OETSolutions/e-ink-weather/work/cad/bez_front.png

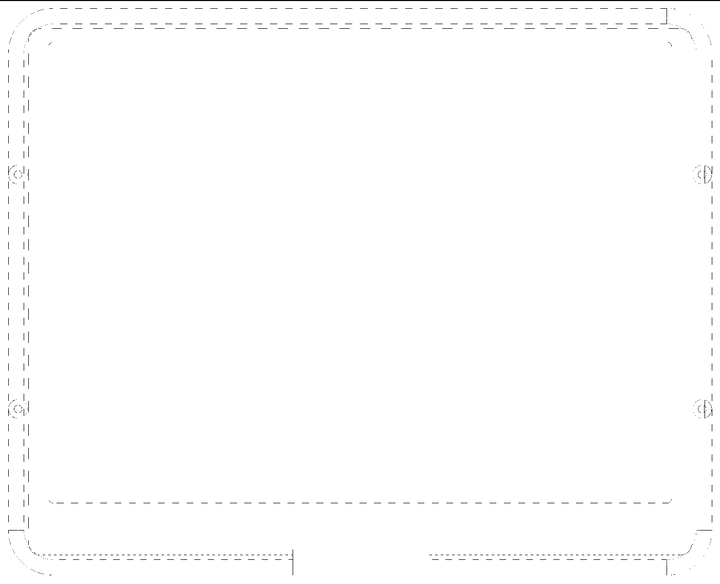
work/cad/bez_front.png
