OETSolutions/e-ink-weather/work/cad/body_iso.png

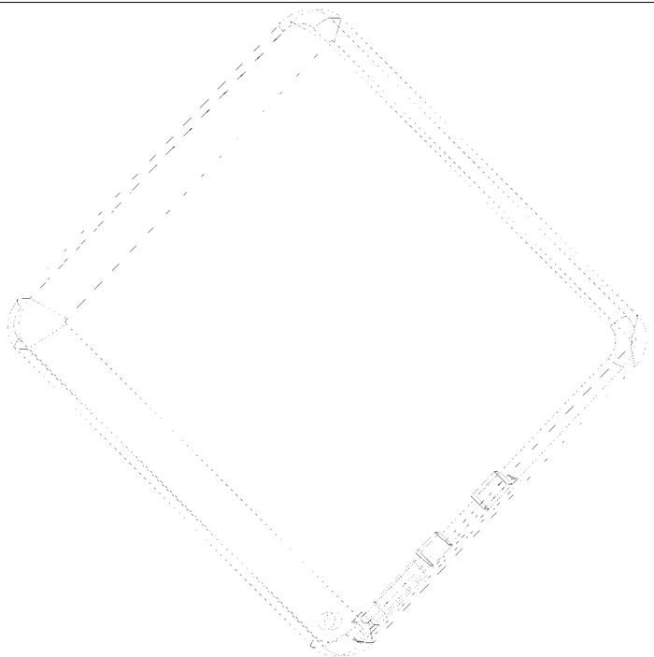
work/cad/body_iso.png
