OETSolutions/e-ink-weather/work/cad/body_side.png

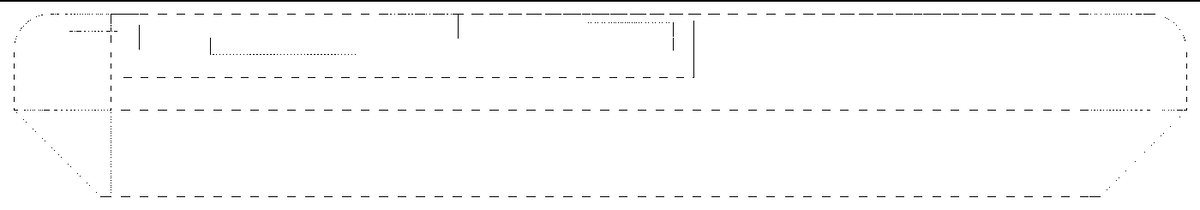
work/cad/body_side.png
