OETSolutions/e-ink-weather/work/cad/ch_iso.png

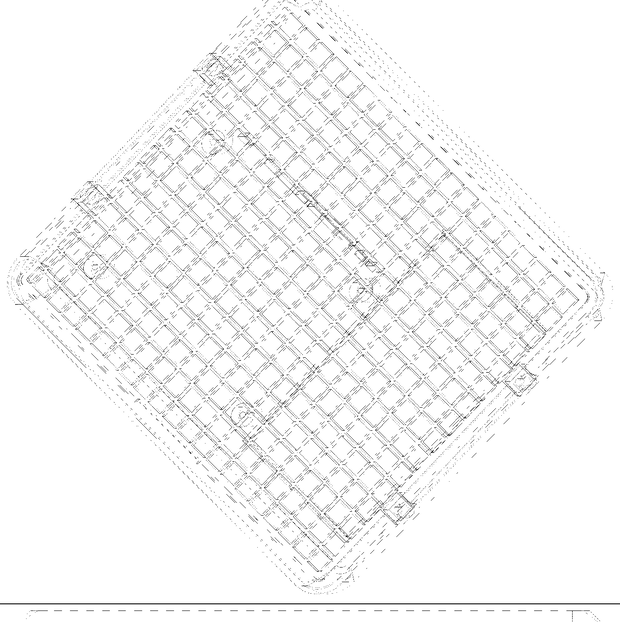
work/cad/ch_iso.png
