OETSolutions/e-ink-weather/work/cad/panel_front.png

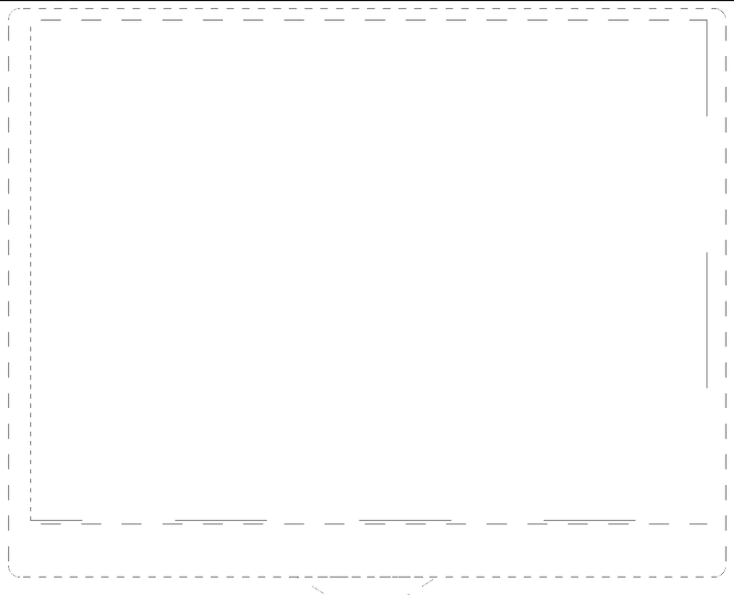
work/cad/panel_front.png
