OETSolutions/e-ink-weather/work/cad/shell_iso2_zoom.png

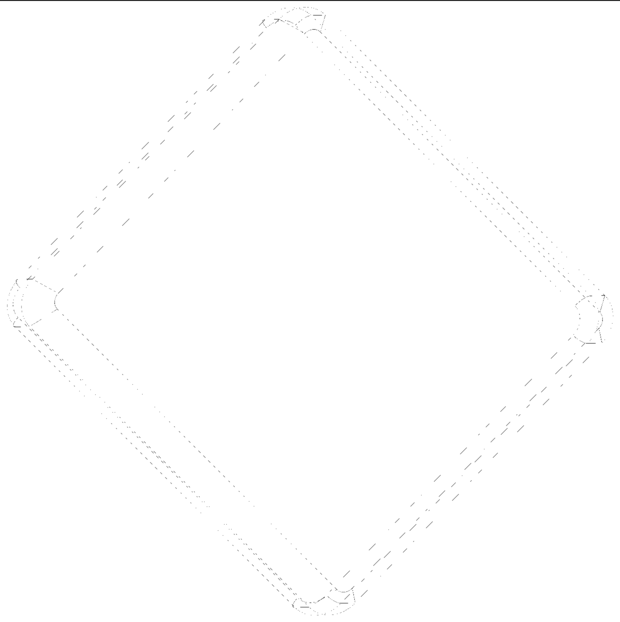
work/cad/shell_iso2_zoom.png
