OETSolutions/e-ink-weather/work/cad/shell_iso_zoom.png

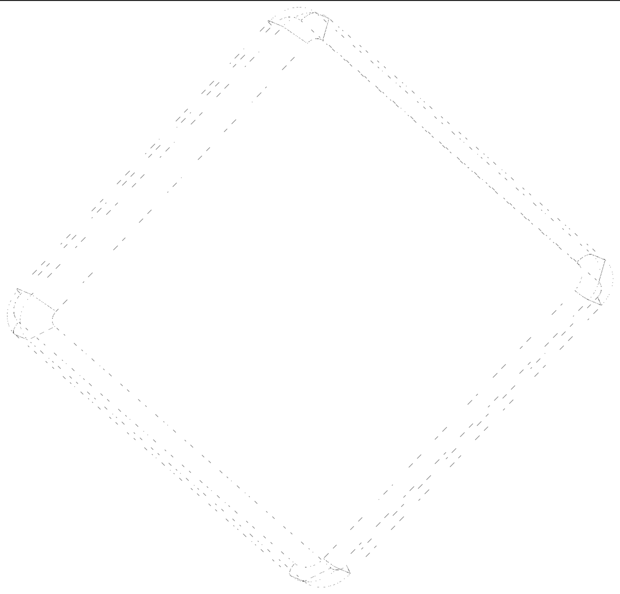
work/cad/shell_iso_zoom.png
