OETSolutions/e-ink-weather/work/cad/shell_side2.png

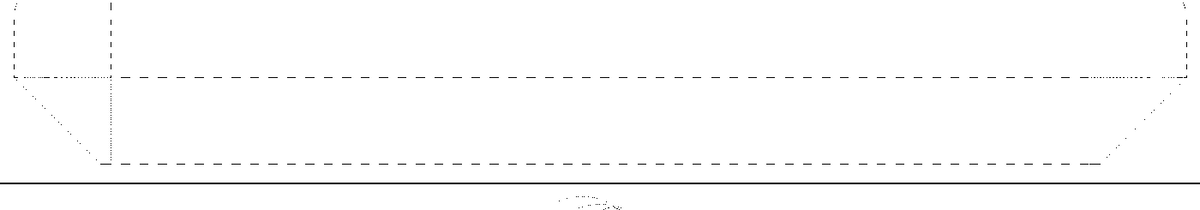
work/cad/shell_side2.png
