OETSolutions/e-ink-weather/work/cad/front_frame.FCStd

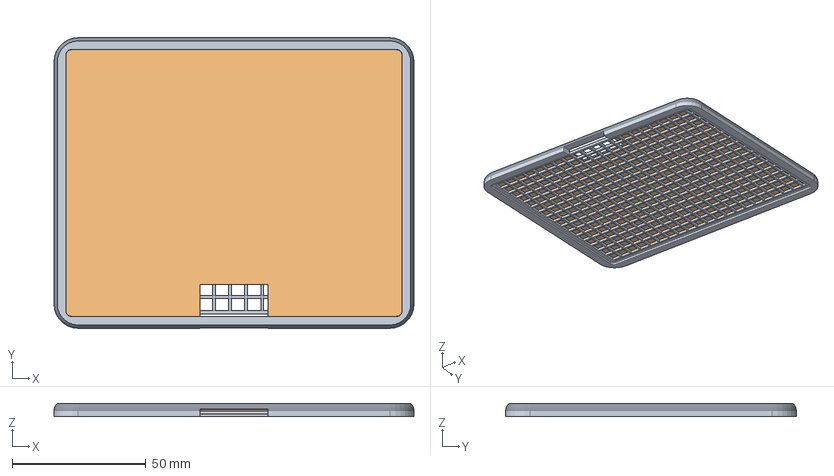
[picture p30: CAD file, 2026-09-19]
work/cad/front_frame.FCStd
134.4 x 108.5 x 4.80 mm
PRINT: Front frame + support grid
CUT: 0.5 mm closed-cell foam backing
