OETSolutions/e-ink-weather/work/cad/panel.FCStd

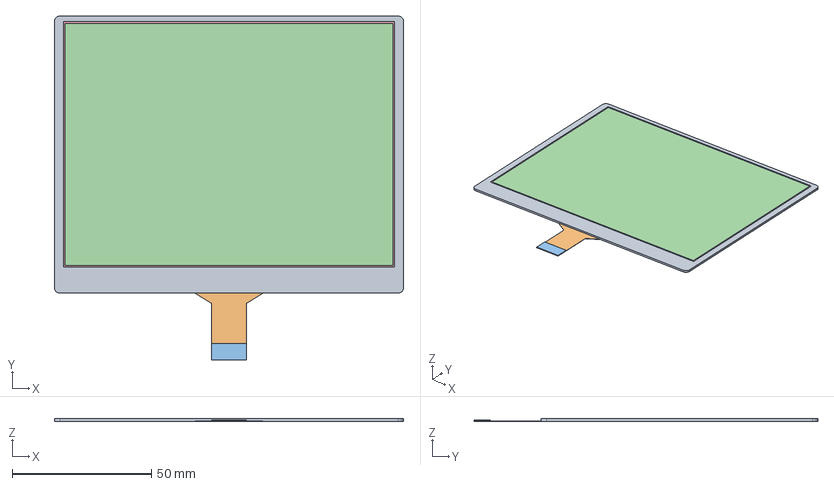
[picture p31: CAD file, 2026-09-19]
work/cad/panel.FCStd
125.4 x 123.5 x 0.902 mm
PANEL_GLASS
PANEL_FPC_TAIL
PANEL_FPC_STIFFENER
PANEL_ACTIVE_AREA
PANEL_BORDER
