OETSolutions/e-ink-weather/code/firmware/components/app/app_refresh.c

#include "app_refresh.h"
#include "api.h"
#include "api_store.h"
#include "canvas.h"
#include "cfg_store.h"
#include "cJSON.h"
#include "datasrc.h"
#include "devcfg.h"
#include "epd.h"
#include "fonts.h"
#include "geo_ip.h"
#include "ha.h"
#include "layout_model.h"
#include "net_http.h"
#include "net_wifi.h"
#include "nvs_keys.h"
#include "owm.h"
#include "provscreen.h"
#include "prov.h"
#include "refresh_policy.h"
#include "render.h"
#include "thermal_guard.h"
#include "value_resolve.h"
#include "widgets.h"
#include "esp_heap_caps.h"
#include "heap_trace.h"
#include "freertos/FreeRTOS.h"
#include "freertos/task.h"
#include "esp_log.h"
#include "esp_system.h"
#include "esp_timer.h"
#include "nvs.h"
#include <string.h>
#include <stdlib.h>

/* The vendor demo reference image, used as the static layer until the web app has uploaded
 * one (Task 21). Declared here rather than included, because it lives in src/ and this is a
 * component — and because it is a placeholder to be deleted, so the dependency should be
 * one line, not an include path. */
/* The boot mark shown when no layout bitmap has been uploaded yet. Generated from the
 * OETSolutions / Aether artwork by tools/gen_boot_logo.py — see that script for the pipeline.
 * This replaced the vendor GoodDisplay demo image, which had no business on a shipped
 * device: it was a bring-up baseline, not artwork. */
extern const uint8_t boot_logo[EPD_FB_BYTES];
/* The header-sized version of the same mark, for the provisioning screen. Generated together
 * with the splash so the two cannot drift apart. */
extern const uint8_t boot_badge[];
extern const int boot_badge_w;
extern const int boot_badge_h;

static const char *TAG = "refresh";

/* How long ensure_static() waits for the freed static-layer region to coalesce before giving up
 * on a tick.
 *
 * MEASURED, NOT GUESSED. When the region is fragmented by a network allocation sitting in the
 * middle of it, the largest free block reads 77,824 — 376 bytes SHORT of the 78,200 a
 * framebuffer needs — and the block walk shows the fragmenter is a handful of 28..132-byte
 * network-stack allocations that free on their own. The pieces then coalesce into one
 * 78,380-byte block, which DOES fit, but the coalesce is not instant: under sustained 2 s HTTP
 * churn the wait was measured acquiring on attempts 16..29, i.e. 800..1,450 ms, with the FIRST
 * acquisition needing longer than the old 5 s ceiling in the worst observed case. So 5 s was
 * marginal and 15 s is a comfortable margin over a 1.45 s measurement.
 *
 * A tick that still cannot get its frame keeps the previous image on the glass, which is the
 * correct FR-29 behaviour, and it RETRIES shortly (see the retry in app_refresh_tick) rather
 * than waiting a whole interval — a stale panel for 15 minutes is the real cost being avoided.
 * On battery this loop is never entered under normal use: the radio is torn down before the
 * render window, so the region is already clean. */
#define FB_ACQUIRE_WAIT_MS 15000
#define FB_ACQUIRE_POLL_MS 50

/* The slot identity meaning "no picture is known to be on the glass", i.e. a partial has no valid
 * base. The three identity spaces are kept disjoint BY CONSTRUCTION:
 *
 *   per-page artwork   -(100 + page*100 + seq)  with page 0..7 and seq 0..99  => -100 .. -899
 *   the legacy bitmap  its live slot number (0 or 1)
 *   the built-in mark  SLOT_BOOT_LOGO (-1000)
 *   unknown            SLOT_NONE (-1)
 *
 * The artwork range has room for 8 pages x 100 sequences, and ARTWORK_MAX_PAGES is 8, so the spaces
 * cannot overlap for any real layout. (An earlier draft used -(100 + page), which left no room for
 * the sequence and collided with the boot mark at page 1 — see load_static_layer_seg for why the
 * sequence is required.)
 *
 * The distinction from SLOT_NONE matters and is NOT a sign test: the artwork sentinel is NEGATIVE,
 * so `slot < 0` is true for every real uploaded layout. See s_shown_slot. */
#define SLOT_NONE      (-1)
#define SLOT_BOOT_LOGO (-1000)

/* The fields to stamp one refresh, and their values. Sized by the parse caps rather than allocated.
 * This is the TICK-LOCAL page, which also carries the parsed widgets and the FR-27 reporting arrays;
 * only the three members a render needs are copied into the cross-tick snapshot below. */
typedef struct {
    layout_widget_t widgets[LAYOUT_MAX_FIELDS];
    value_field_t   fields[LAYOUT_MAX_FIELDS];
    char            values[LAYOUT_MAX_FIELDS][LAYOUT_VALUE_BUF];
    const char     *value_ptrs[LAYOUT_MAX_FIELDS];
    /* The widget id, the RAW reading and whether the drawn string is that number's plain
     * rendering, parallel to values/fields, so GET /api/values (FR-27) can report which box each
     * resolved string belongs to AND let the editor re-format it locally after a format edit. The
     * id is copied rather than pointed at: the widget array is overwritten by the next refresh.
     * `readings`/`rendered_number` are only populated for widgets whose value drew the number —
     * see value_format_widget_rendered(). */
    char            ids[LAYOUT_MAX_FIELDS][API_VALUES_ID_LEN];
    int             has_value[LAYOUT_MAX_FIELDS];
    int             rendered_number[LAYOUT_MAX_FIELDS];
    double          readings[LAYOUT_MAX_FIELDS];
    int             n;              /* how many the page asked for */
    int             n_fields;       /* how many are actually stamped (dynamic only) */
} page_render_t;

/* JUST THE DRAWABLE HALF OF A PAGE: the boxes, their strings, and the count.
 *
 * WHY THIS IS A SEPARATE, SMALL TYPE. The previous frame must be reproducible across ticks, and
 * page_render_t is 9,320 bytes because it also carries the parsed widgets (24 x 288) and the
 * FR-27 reporting arrays — none of which a render reads. Keeping one of those resident costs
 * ~9 KB of .bss, and .bss on this part is DRAM the heap does not get: measured, adding a 9,320-byte
 * static here dropped the largest free block below the 78,200 bytes the static layer needs, so
 * NOTHING could be drawn. The drawable half is 1,640 bytes, which fits. */
typedef struct {
    value_field_t fields[LAYOUT_MAX_FIELDS];
    char          values[LAYOUT_MAX_FIELDS][LAYOUT_VALUE_BUF];
    const char   *value_ptrs[LAYOUT_MAX_FIELDS];
    int           n_fields;
} frame_values_t;

/* What a render needs, pointing at either a live page or the snapshot. `values` is `const char **`
 * rather than `const char *const *` so a live page's array can be used without a cast. */
typedef struct {
    const value_field_t *fields;
    const char *const   *values;
    int                  n_fields;
} frame_spec_t;

/* ONE 78,200-byte buffer, holding the STATIC LAYER of the page currently on the glass — not the
 * composed frame.
 *
 * WHY THE STATIC LAYER AND NOT THE FRAME: a partial refresh passes the SSD2677 the previous and
 * the next frame, because it derives each pixel's transition from the pair. Two frames of 78,200
 * bytes do not fit this part — the only DRAM region large enough for one is 113,840 bytes and the
 * pair needs 156,400 — so a second framebuffer NEVER allocated. Measured on the bench: the
 * transient allocation failed on every refresh and /api/status read `partials_since_full: 0`
 * against `fulls_total: 6`, so FR-11's partial path had never run and every refresh was a full
 * panel flash.
 *
 * Holding the static layer instead makes both frames derivable from ONE buffer: the previous frame
 * is this layer stamped with s_prev_values' strings, and the next frame is the same layer stamped
 * with the current page's values. A partial is only ever taken when the slot identity matches,
 * which means the two frames genuinely share this layer — so it is the right thing to keep.
 *
 * HELD AS SEGMENTS, NOT ONE CONTIGUOUS BUFFER, and that is the whole fix for the render-OOM report
 * (2026-09-22). A single 78,200-byte allocation needs the ONE DRAM region large enough to hold it
 * (0x3ffe4350, 113,840 bytes), and while the HTTP API is live that region is fragmented below
 * 78,200 by a persistent 8,192-byte httpd task stack plus a 16,384-byte app task stack — neither
 * frees, so no wait helps. Held as ~16 KB segments the same bytes come from pieces that always fit
 * (measured: 32,768 bytes allocated fine at the exact moment a 78,200-byte request failed). See
 * segbuf.h.
 *
 * Allocated lazily and FREED ACROSS EVERY FETCH (see app_refresh_tick): the fetch needs contiguous
 * room the segments would otherwise occupy, and a fetch that fails leaves every reading as "--".
 *
 * FREED HERE RATHER THAN IN .bss: as a static array the segments' POINTERS would sit in DRAM that
 * the heap does not get — see the note on the band buffers. */
static segbuf_t s_layer;

/* The strip decoder's state (~11 KB), reserved BY ensure_static() before the segments and released
 * once the layer is loaded (see api_store.h for why the ORDER matters: allocated lazily during the
 * decode it intermittently finds no hole and the strip silently fails). */
static artwork_inflate_t *s_inflate;

/* A segment allocator and releaser for s_layer. Plain internal DRAM, the same capability the old
 * contiguous allocation used. */
static void *layer_seg_alloc(size_t n) { return heap_caps_malloc(n, MALLOC_CAP_8BIT); }
static void  layer_seg_free(void *p)   { free(p); }
/* The identity of the picture on the glass, from load_static_layer_seg(): a NEGATIVE sentinel for
 * per-page artwork (-(100 + page*100 + seq)), the bitmap's slot for the legacy single bitmap, SLOT_BOOT_LOGO
 * for the built-in boot mark, SLOT_NONE when nothing is known. Compared for equality to decide
 * whether a partial is valid.
 *
 * IT MUST NOT DOUBLE AS THE "IS ANYTHING ON THE GLASS" FLAG, and that is a bug this code had: the
 * artwork sentinel is negative, so `s_shown_slot < 0` was true for every real uploaded layout and
 * every tick read "nothing on the glass" and forced a FULL refresh — which is exactly why
 * /api/status showed `partials_since_full: 0` no matter what the partial budget said. The two
 * questions are different and now have different answers: identity here, presence in
 * s_glass_present below. */
static int      s_shown_slot = SLOT_NONE;
/* Non-zero once a push has put an image on the glass and nothing has overwritten or dropped it
 * since. This, not the sign of the slot, is what refresh_decide() means by "something is on the
 * glass to diff against". */
static int      s_glass_present;

/**
 * Static layer ownership: one mutex guarding the 78,200-byte resident layer.
 *
 * WHY THIS EXISTS. The OTA path opens a TLS connection from an HTTP handler — the httpd task —
 * while the render task holds the layer resident between ticks. The handshake needs the ONE
 * contiguous DRAM region large enough for a framebuffer (see the release reasoning below), so
 * with the layer held it fails outright:
 *
 *     esp-tls-mbedtls: mbedtls_ssl_setup returned -0x7F00   (ALLOC_FAILED)
 *     api_ota: manifest fetch failed: ESP_ERR_HTTP_CONNECT
 *
 * measured on the bench 2026-09-24 — every OTA check returned 502 in ~0.12 s, which is the
 * tell that no handshake was ever attempted. The refresh path avoids this by releasing the
 * layer before its own fetches; the OTA handlers cannot, because they run on a DIFFERENT task
 * and must not free memory the render task is in the middle of reading.
 *
 * So ownership is explicit: the whole tick holds this lock, and a fetcher outside the render
 * path takes it (waiting for any tick in flight), drops the layer, does its TLS work, and gives
 * it back. One lock, one rule — see app_fetch_pause().
 */
static SemaphoreHandle_t s_layer_mutex;

static void layer_lock(void)
{
    /* Created on first use rather than in app_main: this file has no init function and the
     * first caller may be either task. xSemaphoreCreateMutex has no failure mode worth
     * branching on here beyond allocation, and a failure to allocate a mutex on a heap that
     * must hold a 78 KB framebuffer means the device has far larger problems. */
    if (!s_layer_mutex) {
        static portMUX_TYPE mux = portMUX_INITIALIZER_UNLOCKED;
        portENTER_CRITICAL(&mux);
        if (!s_layer_mutex) s_layer_mutex = xSemaphoreCreateMutex();
        portEXIT_CRITICAL(&mux);
    }
    if (s_layer_mutex) xSemaphoreTake(s_layer_mutex, portMAX_DELAY);
}

static void layer_unlock(void)
{
    if (s_layer_mutex) xSemaphoreGive(s_layer_mutex);
}

/* Every return in the tick must land here so the layer is never left un-released on an error
 * path — a layer held by a returned tick would block every later fetch pause. */

/* The values that were stamped into the frame now on the glass, so the PREVIOUS frame can be
 * recomposed for a partial. This is the whole reason a partial is possible here: the previous
 * frame is not stored (two frames do not fit), it is REPRODUCED from the resident static layer
 * plus these values, and 24 strings of 40 bytes is 1.6 KB rather than 78,200. */
static frame_values_t s_prev_values;
static int            s_have_prev_values;   /* 0 until a push has recorded what it drew */

/* Allocate the resident static layer, as SEGMENTS. Returns 0 on success, -1 on failure.
 *
 * SEGMENTATION IS THE FIX for the render-OOM report: a single 78,200-byte request needs the one
 * DRAM region large enough to hold it, and the live HTTP API fragments that region below 78,200
 * with allocations that never free. Small segments are always placeable. The sizes are tried
 * largest-first (16 KB down to 2 KB) so the common case keeps the segment count low and the band
 * reader's inner loop short; a fragmented heap simply settles on smaller pieces.
 *
 * NO INFLATE WINDOW IS RESERVED HERE. The artwork is stored as independent per-strip zlib streams
 * (see lib/upload/artwork.h), so loading it needs no 32 KB dictionary: only a strip-sized output
 * buffer and a ~11 KB decompressor that lives on the caller's stack. An earlier single-stream
 * version reserved a ~44 KB window BEFORE the segments, and that window could only fit the same
 * large region the segments need — measured at tick 2 with WiFi up, segments + window did not fit
 * in either order, and the window was also LEAKED on a failed acquire, so every later tick failed
 * too. Removing the window removes both faults.
 *
 * WHY IT STILL WAITS (bounded) BEFORE GIVING UP: a tick that cannot get the layer has to leave the
 * last good image up (FR-29) and try again shortly. The wait lets a genuinely transient fragmenter
 * clear, but the segmented allocator makes the wait almost never necessary — a contiguous 78,200
 * could fail outright where the segmented form succeeds on the first try. */
static int ensure_static(void)
{
    if (s_layer.n > 0) return 0;

    /* RESERVE THE DECOMPRESSOR FIRST — see s_inflate and api_store.h for why the ORDER is
     * load-bearing. On failure, release whatever was taken so the next tick retries cleanly: a
     * window leaked here would be memory every later tick needs, which is exactly how the earlier
     * single-stream version wedged (it reserved the window and returned without giving it back). */
    if (!s_inflate) s_inflate = artwork_inflate_reserve();

    /* BOUNDED WAIT — this is load-bearing and was briefly lost in the segmented rewrite.
     *
     * A single attempt is not enough because the region is fragmented by TRANSIENT network-stack
     * allocations that free on their own: measured, the largest free block sits below what the
     * layer needs for up to ~1.45 s after a fetch, then coalesces. Without this loop such a tick
     * fails outright, records an OOM and leaves the panel stale even though the memory returns a
     * moment later — the exact "reports failure while the device is fine" class FR-29 exists to
     * avoid. segbuf_alloc() frees every partial segment it took before returning, so retrying it
     * leaks nothing. The cost is paid ONLY on a losing tick: a healthy tick returns on the first
     * attempt having waited nothing. See FB_ACQUIRE_WAIT_MS for the measurement behind the ceiling. */
    const int64_t deadline_us = esp_timer_get_time() + (int64_t)FB_ACQUIRE_WAIT_MS * 1000;
    if (s_inflate) {
        for (;;) {
            if (segbuf_alloc(&s_layer, EPD_FB_BYTES, 16384u, 2048u,
                             layer_seg_alloc, layer_seg_free) == 0) {
                return 0;
            }
            if (esp_timer_get_time() >= deadline_us) break;
            vTaskDelay(pdMS_TO_TICKS(FB_ACQUIRE_POLL_MS));
        }
    }

    /* A failure here means the heap has no room for the layer at all (the decompressor is tiny by
     * comparison and is not the limiting factor). Give the window back so the retry starts clean. */
    artwork_inflate_release(s_inflate);
    s_inflate = NULL;
    ESP_LOGE(TAG, "cannot allocate the static layer (%u bytes in %u-byte segments) "
                  "(free heap %u, largest block %u)",
             (unsigned)EPD_FB_BYTES, 2048u,
             (unsigned)esp_get_free_heap_size(),
             (unsigned)heap_caps_get_largest_free_block(MALLOC_CAP_8BIT));
    HEAP_DUMP("segmented static layer allocation failed");
    HEAP_BLOCKS("segmented static layer allocation failed");
    return -1;
}

/* A WHOLE-CONTIGUOUS static layer, for the one caller that cannot use segments: the provisioning
 * screen draws a full frame into a single buffer and hands it to epd_write_frame(). That path runs
 * BEFORE api_start() on a fresh heap, where a contiguous 78,200 bytes is available. Kept separate
 * from ensure_static() so the render path never regresses to requiring contiguity. */
static uint8_t *s_static_contig;

static int ensure_static_contiguous(void)
{
    if (s_static_contig) return 0;
    s_static_contig = heap_caps_malloc(EPD_FB_BYTES, MALLOC_CAP_8BIT);
    if (!s_static_contig) {
        ESP_LOGE(TAG, "cannot allocate a contiguous static layer for the setup screen "
                      "(%u bytes) (free heap %u, largest block %u)",
                 (unsigned)EPD_FB_BYTES,
                 (unsigned)esp_get_free_heap_size(),
                 (unsigned)heap_caps_get_largest_free_block(MALLOC_CAP_8BIT));
        return -1;
    }
    return 0;
}

/* The band reader over the segmented layer: the renderer pulls the static layer through this, so
 * it never needs the layer to be contiguous. */
static int seg_reader(void *ctx, size_t offset, uint8_t *dst, size_t len)
{
    return segbuf_read((const segbuf_t *)ctx, offset, dst, len);
}

/* Set when a tick could not get its static layer and therefore drew nothing. The image
 * on the glass is still the last good one (correct FR-29 behaviour), but the region may stay
 * fragmented for far longer than the acquire wait — measured: a state that held the largest
 * block at ~38 KB for 30 s+ with only ~230 bytes of small USED blocks in the way. So the serve
 * loop retries promptly on this flag, via the pending-refresh request, rather than leaving the
 * panel stale for a whole interval. A full refresh is requested because there is no resident
 * diff base left. */
static volatile int s_fb_lost;

int app_refresh_frame_lost(void) { return s_fb_lost; }

/* The last temperature this device successfully fetched, and when.
 *
 * WHY IT IS REMEMBERED: a failed fetch must not blank the reading. Without this, an OWM
 * outage would replace a real temperature with "--" on the next render — and since a bitmap
 * upload also triggers a render (so the web app can see what it uploaded), a user who had
 * just pushed a new layout would watch their temperature disappear for reasons that have
 * nothing to do with the layout. Keeping the last value means a transient network failure
 * costs nothing on the glass, which is the same principle as FR-29's last-good image.
 *
 * See s_last_current, declared further down, for what is actually kept. */


/* The last successful full refresh, for the datasheet's 24 h rule. Only full refreshes set
 * it: a partial does not clear ghosting, so it cannot postpone the need for one.
 *
 * Deliberately NOT persisted across deep sleep. The panel's own glass holds the image across
 * a sleep, but the RTC keeps counting, so this stays meaningful for a device that sleeps.
 * A cold boot resets it to 0, which makes the first refresh a full one — the safe default,
 * since the firmware cannot know what a power cut left on the glass. */
static int64_t s_last_full_us;

/* Whole hours since the last full refresh. 0 before the first one, which refresh_decide()
 * treats as "refresh fully" anyway. */
static int hours_since_full(void)
{
    if (s_last_full_us == 0) return 0;
    const int64_t h = (esp_timer_get_time() - s_last_full_us) / 3600000000LL;
    return h > 24 ? 24 : (int)h;    /* clamp: past the boundary the exact value is moot */
}

/* Pull the static layer into `dst`. Returns 0 on success.
 *
 * Preference order: the page's OWN artwork, then the single legacy bitmap, then the built-in boot
 * mark. A device that has never had anything pushed still renders something meaningful rather
 * than a blank panel (FR-29).
 *
 * `page` IS WHAT MAKES ROTATION CORRECT. With one shared layer (the old behaviour), a rotating
 * page stamped its readings onto ANOTHER page's artwork — page 2's "TOMORROW HIGH" label sitting
 * over page 1's temperature — which was seen on hardware. The page's own picture is therefore
 * tried FIRST, and only a page that genuinely has none falls back. */
static int load_static_layer_seg(segbuf_t *b, int page, int *from_slot)
{
    /* The artwork identity is taken ONCE, BEFORE the load, and used whatever the load returns: a
     * promote that lands between this read and the load would otherwise make the identity describe a
     * different set from the pixels just read. A promote always follows with
     * api_request_full_refresh(), so a stale identity here can only cost a full refresh, never
     * authorise a partial against the wrong picture. */
    int aw_pages = 0;
    uint32_t aw_seq = 0;
    artwork_store_identity(&aw_pages, &aw_seq);

    if (s_inflate && artwork_store_load_page_seg(page, b, s_inflate) == 0) {
        /* THE IDENTITY MUST INCLUDE BOTH THE PAGE AND THE SET'S SEQUENCE.
         *
         * The PAGE, because a partial is only valid when the frame on the glass and the frame about
         * to be drawn are the same picture — and during rotation the previous frame is the PREVIOUS
         * PAGE's artwork. A single shared sentinel for every page would make a page change look like
         * an unchanged source and scribble fragments of page 1's layout onto page 2's.
         *
         * The SEQUENCE, because the page index alone cannot see an UPLOAD. Pushing a new layout for
         * the page that is already on the glass leaves the page index — and therefore an identity
         * derived only from it — completely unchanged, while the picture underneath changes. A
         * partial would then diff the new layout against the old one, ghosting the previous layout
         * behind the new text. The sequence increments on every promote, so an upload changes the
         * identity and forces the full refresh api_request_full_refresh() already requests. Without
         * it, that request is the ONLY thing standing between an uploaded layout and a wrong diff.
         *
         * Mixed into the negative range so it cannot collide with the bitmap slots (0/1),
         * SLOT_BOOT_LOGO (-1000), or SLOT_NONE (-1): a page P with sequence S is
         * -(100 + P*100 + S), which for the 8 possible pages and 100 sequences stays inside
         * -100..-899 and never reaches the boot mark. See the SLOT_* definitions. */
        const int seq = (int)(aw_seq % 100u);
        *from_slot = -(100 + page * 100 + seq);
        return 0;
    }
    /* A page with no artwork of its OWN falls back rather than borrowing a neighbour's: the wrong
     * labels on the glass are worse than none. `aw_pages` is unused here — the fallbacks below have
     * their own identities. */
    (void)aw_pages;
    if (bitmap_store_load_seg(b) == 0) {
        *from_slot = api_live_bitmap_slot();
        return 0;
    }
    /* The built-in boot mark is a const array in flash, so it is copied in — a segmented write per
     * 4 KB rather than one memcpy. It is REPRODUCIBLE, so it gets a real identity of its own rather
     * than SLOT_NONE: it must not share -1 with "unknown", because the two mean opposite things —
     * this one can be a valid diff base, and a partial of the boot mark against itself is a genuine
     * no-op rather than corruption. */
    for (size_t off = 0; off < EPD_FB_BYTES; off += 4096u) {
        size_t n = EPD_FB_BYTES - off;
        if (n > 4096u) n = 4096u;
        if (segbuf_write(b, off, boot_logo + off, n) != 0) return -1;
    }
    *from_slot = SLOT_BOOT_LOGO;
    return 0;
}

/* ------------------------------------------------------------------------------------------
 * THE LAYOUT IS THE WEB APP'S, NOT THE FIRMWARE'S
 *
 * This used to be `static const value_field_t DEFAULT_FIELDS[2]` — two boxes at fixed
 * coordinates, stamped with a temperature and a "--". The device therefore rendered a layout
 * nobody had authored: a user's pushed layout was parsed for scheduling only and then thrown
 * away, so every widget but the current temperature was blank, and the one reading that did
 * appear sat in a box the user had not drawn.
 *
 * The boxes now come from the document (lib/layout/src/widgets.c), the values from
 * lib/layout/src/value_resolve.c, and the page from the rotation schedule. The firmware still
 * never INVENTS a position or a label — it stamps the readings the web app's layout asked for
 * (FR-1). Keeping that property is what lets a layout change ship with no firmware update.
 * ------------------------------------------------------------------------------------------ */

/* Turn the parsed widgets into the renderer's field/value arrays.
 *
 * Only DYNAMIC widgets are stamped: a 'static' widget is baked into the bitmap by the web app
 * and stamping it again would put a reading on top of the chrome. */
static void build_fields(page_render_t *p, const value_sources_t *src,
                         char (*ids)[48], int n_ids, long now)
{
    int nf = 0;
    for (int i = 0; i < p->n; i++) {
        const layout_widget_t *w = &p->widgets[i];
        if (w->role != 'd') continue;
        if (w->w <= 0 || w->h <= 0) continue;       /* nothing to clip to */

        value_field_t *f = &p->fields[nf];
        f->x = w->x; f->y = w->y; f->w = w->w; f->h = w->h;
        f->align_h = w->align_h;
        f->align_v = w->align_v;
        f->font_id = w->font_id;
        /* A widget bound to OWM's icon field draws the CONDITION ICON for the value rather than
         * the value's text. The resolved value is the OWM code ("04n"); a text field would print
         * that code on the glass, and an icon field maps it to a picture (see weather_icons.h).
         * Only owm-current carries an icon — a daily forecast binding has no icon code to map. */
        f->kind = (w->binding.kind == BIND_OWM_CURRENT &&
                   w->binding.owm_field == OWM_F_ICON)
                ? VALUE_KIND_ICON : VALUE_KIND_TEXT;

        /* The buffer is per-field and the pointer array is parallel to `fields`, because
         * render_compose_stream() takes `const char *const *` and does not own the strings. */
        datasrc_value_t v;
        p->has_value[nf] = value_format_widget_rendered(w, src, ids, n_ids, now, &v,
                                                        &p->rendered_number[nf],
                                                        p->values[nf], sizeof(p->values[nf]));
        /* THE RAW READING, but only when the drawn text really is that number's plain rendering:
         * the endpoint reports it so the editor can re-format after a format edit, and re-format
         * would be wrong for an alert word, a text state or an icon code (see
         * value_format_widget_rendered). */
        p->readings[nf] = v.value;
        p->value_ptrs[nf] = p->values[nf];
        /* The widget's own id travels with the value, for GET /api/values (FR-27): the editor
         * previews the REAL fetched data by asking the device what it resolved, and without the
         * id the app could not tell which box a string belongs to. */
        strncpy(p->ids[nf], w->id, sizeof(p->ids[nf]) - 1);
        p->ids[nf][sizeof(p->ids[nf]) - 1] = '\0';
        nf++;
    }
    p->n_fields = nf;
}

/* ------------------------------------------------------------------------------------------
 * PUSHING A FRAME OUT OF ONE STATIC LAYER
 *
 * A partial refresh hands the SSD2677 the frame CURRENTLY ON THE GLASS and the frame it should
 * show next, and the controller derives each pixel's transition from the pair. That pair is why
 * FR-11's partial path had never run on this hardware: two 78,200-byte frames do not fit — the
 * only DRAM region large enough for one is 113,840 bytes and the pair needs 156,400 — so the
 * second framebuffer failed to allocate on EVERY refresh. Measured on the bench: the transient
 * allocation failed on every attempt and /api/status read `partials_since_full: 0` against
 * `fulls_total: 6`, so every refresh was a full panel flash and the whole FR-11 strategy was
 * dead code that reported success.
 *
 * The frames are therefore not STORED, they are REPRODUCED. One buffer holds the page's static
 * layer (the picture the web app uploaded, the expensive half at 78,200 bytes); the values that
 * were stamped on it last time live in s_prev_values, which is 1.6 KB. Stamping
 * those strings onto the layer gives the frame on the glass, and stamping the new values
 * gives the next frame — so both are produced a BAND at a time, into two buffers of
 * RENDER_BAND_ROWS rows each, and neither whole frame ever exists in RAM.
 *
 * The layer must be the SAME for both frames, which is guaranteed rather than assumed: the caller
 * passes `partial` only when the slot identity matches (see app_refresh_tick), and a slot encodes
 * the picture (load_static_layer_seg). Different page, different artwork, different bitmap => a full
 * refresh, because a partial across two unrelated pictures would leave ghosted fragments of the
 * old layout on the glass.
 *
 * WHY THE BAND BUFFERS ARE ALLOCATED PER PUSH AND FREED AGAIN: this part has exactly one region
 * large enough for the static layer, and that region is what the TLS handshake needs on every
 * fetch. A permanently-held band pair is memory the radio cannot have at boot — the exact
 * starvation that leaves an unprovisioned device unable to be set up (see app_fbs_reserve()).
 * Held only inside the push, they cost nothing the radio can see. */

/* The band size, in rows. 136 divides 680 exactly, giving 5 bands and a 15,640-byte buffer each —
 * the LEAST work per push, which is why it is the first choice. It is only the first choice,
 * though: on USB the radio keeps running for the API (FR-31), and the static layer plus the radio's
 * own allocations leave the largest free block around 14,848 bytes — measured on the bench, 792
 * bytes SHORT of a 15,640-byte band, so the push failed with ESP_ERR_NO_MEM on every tick. Rather
 * than pin the band to whatever happens to fit today, the size is found by TRIAL: halve it until
 * both buffers fit. Each halving is a divisor of 680 down to 8 (680 = 2^3 * 5 * 17), so no band is
 * ever an awkward fraction.
 *
 * A smaller band is not a correctness change — the driver walks whatever rows it is given and the
 * compose is row-exact — it only costs more callback invocations. */
#define RENDER_BAND_ROWS_MAX 136
#define RENDER_BAND_ROWS_MIN 8

/* What a band provider needs: the static layer, the two value sets, the band geometry, and the
 * scratch buffers the composes read out of. */
typedef struct {
    uint8_t            *prev_band;      /* composed: what is on the glass */
    uint8_t            *next_band;      /* composed: what it should show */
    const frame_spec_t *next;
    const frame_spec_t *prev;           /* NULL for a full refresh: no previous frame is read */
    int                 band_rows;      /* the size this push settled on (see above) */
} band_push_t;

/* The driver's band provider (epd_band_fn).
 *
 * IT IS CALLED IN DESCENDING BAND ORDER — the panel scans bottom-up, so the last band goes out
 * first — and it must write its band where the driver expects it, which is why it returns the rows
 * it produced and the driver cross-checks against the rows that band actually has.
 *
 * `prev` may be NULL for a full refresh: the previous frame is never read then (a full expands the
 * next frame alone), so composing it would be wasted work — and, worse, a wasted band buffer.
 *
 * Returns 0 on success. A compose failure propagates as a non-zero return, which the driver turns
 * into ESP_ERR_INVALID_STATE and the caller into a failed push that leaves the old image up. */
static int band_provider(void *ctx, int band_index,
                         uint8_t *prev_out, uint8_t *next_out, int *rows_out)
{
    band_push_t *b = (band_push_t *)ctx;
    const int y0 = band_index * b->band_rows;
    const int rows = (EPD_HEIGHT - y0 < b->band_rows) ? (EPD_HEIGHT - y0) : b->band_rows;

    canvas_t c;

    canvas_init_band(&c, b->next_band, y0, rows);
    if (render_compose_band(&c, seg_reader, &s_layer,
                            b->next->fields, b->next->values, b->next->n_fields) != 0) {
        return -1;
    }

    if (b->prev) {
        canvas_init_band(&c, b->prev_band, y0, rows);
        if (render_compose_band(&c, seg_reader, &s_layer,
                                b->prev->fields, b->prev->values, b->prev->n_fields) != 0) {
            return -1;
        }
    }

    *rows_out = rows;
    (void)prev_out;     /* the driver hands us the buffers we already have in `b` */
    (void)next_out;
    return 0;
}

/* Push the composited page, band by band, out of the resident static layer. Returns ESP_OK, or an
 * error the caller surfaces and records without changing the glass.
 *
 * `partial` selects the wire format AND how much is composed: a partial needs the previous frame as
 * well, a full does not. The band buffers are taken here, because only the caller knows whether the
 * partial path is live yet — and they are freed on every exit, including the failures, because a
 * leaked pair is memory the next fetch's TLS handshake needs. */
static int push_banded(const frame_spec_t *next, const frame_spec_t *prev, int partial)
{
    /* Find the largest band that fits, by trial. See RENDER_BAND_ROWS_MAX for why the size cannot
     * be a constant. The two buffers are taken together and released together, so a size where only
     * one fits is not accepted: a partial needs the pair, and settling for a size that cannot hold
     * both would turn every partial into a full refresh — silently, which is the failure this whole
     * change exists to remove. */
    uint8_t *prev_band = NULL;
    uint8_t *next_band = NULL;
    int band_rows = 0;

    for (int r = RENDER_BAND_ROWS_MAX; r >= RENDER_BAND_ROWS_MIN; r /= 2) {
        const size_t bytes = (size_t)r * EPD_PITCH;
        next_band = heap_caps_malloc(bytes, MALLOC_CAP_8BIT);
        if (!next_band) continue;
        if (!partial) { band_rows = r; break; }
        prev_band = heap_caps_malloc(bytes, MALLOC_CAP_8BIT);
        if (prev_band) { band_rows = r; break; }
        /* Only one fitted, so this size is no good for a partial: give the buffer back and try the
         * next size down rather than leaking it and failing. */
        free(next_band);
        next_band = NULL;
    }

    if (!next_band) {
        ESP_LOGE(TAG, "no band buffer fits (largest block %u); the %s refresh cannot be drawn",
                 (unsigned)heap_caps_get_largest_free_block(MALLOC_CAP_8BIT),
                 partial ? "partial" : "full");
        free(prev_band);
        return ESP_ERR_NO_MEM;
    }

    band_push_t b = {
        .prev_band = prev_band,
        .next_band = next_band,
        .next = next,
        /* A full refresh composes the next frame only, so the previous VALUES are not needed —
         * and passing them anyway would make the provider compose a second frame for the sole
         * purpose of the driver ignoring it. */
        .prev = partial ? prev : NULL,
        .band_rows = band_rows,
    };

    /* The driver is told the SAME band geometry the buffers were sized for; the two must agree or
     * it would walk past the end of a buffer. */
    const esp_err_t e = epd_write_frame_banded(band_provider, &b, prev_band, next_band,
                                               band_rows, partial);
    free(prev_band);
    free(next_band);
    return e;
}

/* The last temperature this device successfully fetched, and when.
 *
 * WHY IT IS REMEMBERED: a failed fetch must not blank the reading. Without this, an OWM outage
 * would replace a real temperature with "--" on the next render — and since a bitmap upload also
 * triggers a render (so the web app can see what it uploaded), a user who had just pushed a new
 * layout would watch their temperature disappear for reasons that have nothing to do with the
 * layout. Keeping the last value means a transient network failure costs nothing on the glass,
 * which is the same principle as FR-29's last-good image.
 *
 * It is the CURRENT CONDITIONS document that is kept rather than a formatted string: the widgets
 * bind to different fields of it (temp, humidity, wind, condition), so remembering the parsed
 * string would only serve whichever widget happened to be first. */
static char s_last_current[2048];
static int  s_have_last_current;

/* ---- The split interval: OWM documents retained between fetches ----------------
 *
 * WHY THE OWM SIDE NEEDS ITS OWN CACHE. The two data sources have different cadences and costs:
 * Home Assistant is the user's own server (no quota, changes in seconds), while OWM publishes
 * only ~every 10 minutes and the free tier caps calls at 1000/day. When `owmUpdateSeconds` is
 * longer than `updateSeconds`, the tick still runs at the fast rate for HA but must NOT re-fetch
 * OWM — and it must still draw the OWM values, because OWM has not changed them. Drawing them
 * means resolving them from the documents again, so the documents have to survive the tick.
 *
 * The CURRENT-conditions document is already retained (s_last_current, above) for the fetch-failure
 * fallback, so that half costs nothing new. The FORECAST document is the one that used to be a
 * transient heap buffer freed at the end of every tick; it is kept here instead.
 *
 * ALLOCATED LAZILY, ONLY WHEN THE SPLIT IS ACTIVE. A device whose owmUpdateSeconds equals its
 * updateSeconds (the default, and every pre-split config) fetches OWM every tick and needs no
 * cache at all, so it keeps today's exact memory profile: a transient fetch buffer that is gone
 * before the render window opens. Only a device that actually asked for the split pays the
 * resident bytes — and it is the render window's contiguous DRAM that pays, which is why this is
 * gated rather than always-on. See ensure_forecast_cache(). */
static char  *s_forecast_cache;         /* retained forecast document, or NULL */
static size_t s_forecast_cap;           /* its capacity in bytes; 0 = not allocated */
static int    s_have_forecast_cache;    /* 0 until a fetch has landed in it */
static int64_t s_last_owm_fetch_us;     /* when OWM was last fetched; 0 = never this boot */

/* HW-1's operating-temperature guard.
 *
 * The panel datasheet gives TOPR 0..50 C and warns that drawing outside it produces garbage;
 * HW-1 requires the firmware to "surface a warning state rather than render garbage". The guard
 * has existed and been host-tested since Task 6b, but was never CALLED from the render path —
 * so the requirement was unmet on the device.
 *
 * `valid` is false whenever the sensor is unusable, which on this hardware is ALWAYS: the
 * SSD2677's 0x40 register reads a constant -15 C regardless of ambient (measured 2026-09-18, see
 * the spec's HW-1 note). Feeding that constant in with valid=1 would report TOO_COLD on a warm
 * bench and block every render, which is precisely the failure the guard's fourth state exists to
 * prevent. So the reading is validated against the known-stuck constant and only a reading that
 * has actually MOVED is trusted.
 *
 * Returns 1 when the render must be skipped (genuinely out of range), 0 otherwise — including
 * THERMAL_UNKNOWN, where HW-1 says render and log rather than block. */
static int thermal_blocks_render(void)
{
    static int s_boot_c = 0;
    static int s_have_prev = 0;

    int t = 0;
    const int valid = (epd_read_temp(&t) == ESP_OK);

    if (!valid) {
        if (!s_have_prev) {
            ESP_LOGW(TAG, "panel temperature unreadable; guard cannot decide, rendering");
            s_have_prev = 1;
        }
        return 0;
    }

    /* The first usable reading is remembered but cannot be classified: one sample cannot be told
     * apart from a stuck constant. It is logged so the value is on the record. */
    if (!s_have_prev) {
        s_boot_c = t;
        s_have_prev = 1;
        ESP_LOGI(TAG, "panel temperature %d C (first reading; guard needs a second to trust it)", t);
        return 0;
    }

    /* A sensor that never changes is the known-stuck case, and must not gate the render. */
    if (t == s_boot_c) {
        return 0;
    }

    const thermal_state_t th = thermal_check(t, 1);
    if (th == THERMAL_TOO_COLD || th == THERMAL_TOO_HOT) {
        ESP_LOGE(TAG, "panel temperature %d C is outside the 0..50 C operating range; "
                      "skipping this refresh (HW-1)", t);
        api_note_error(th == THERMAL_TOO_COLD ? "thermal: too cold to render"
                                              : "thermal: too hot to render");
        return 1;
    }
    return 0;
}

esp_err_t app_render_last_good(void)
{
    /* BOOT PATH ONLY, and therefore deliberately unlocked. This runs before api_start(), which
     * is the only thing that can reach app_fetch_pause(), so no pause can overlap it and the
     * lock would only add a call that can never contend. Do NOT call this once the API is
     * serving — use app_refresh_tick() (which holds the lock) instead. */
    if (ensure_static() != 0) return ESP_ERR_NO_MEM;

    /* Page 0: the boot path shows the last-good image before the network, and it cannot know
     * which page was on the glass when the device slept. Page 0 is the defined default (a
     * single-page layout renders identically at any index). */
    int slot = SLOT_NONE;
    if (load_static_layer_seg(&s_layer, 0, &slot) != 0) {
        return ESP_ERR_INVALID_STATE;
    }
    /* The strip decoder has done its job for this load — give the ~11 KB back before the band
     * buffers are taken, so the push has the room. It is re-reserved on the next ensure_static(). */
    artwork_inflate_release(s_inflate);
    s_inflate = NULL;

    /* No live values yet (this runs before the network), so the frame is the static layer alone.
     * That is the point: FR-29 wants the last good image visible immediately, not a blank panel
     * during the fetch, and the values from the previous power cycle are not recoverable — the RAM
     * that held them did not survive the sleep. So this is the bare picture, and a device that has
     * never fetched shows exactly that rather than a placeholders frame.
     *
     * No values are recorded as the previous frame for the same reason: a later partial must
     * reproduce THIS frame as its "previous" one, and this frame has nothing stamped on it. */
    const frame_spec_t none = { .fields = NULL, .values = NULL, .n_fields = 0 };
    const esp_err_t e = push_banded(&none, NULL, 0);
    if (e != ESP_OK) {
        ESP_LOGE(TAG, "panel write failed: %s", esp_err_to_name(e));
        api_note_error("render: panel write failed");
        return e;
    }

    /* This frame is now on the glass, so it becomes the "previous" frame a later partial refresh
     * is diffed against — recorded as its VALUES, not as 78,200 bytes, because two whole frames do
     * not fit this part (see the block comment above push_banded). */
    s_prev_values.n_fields = 0;
    s_shown_slot = slot;
    s_glass_present = 1;
    s_have_prev_values = 1;
    api_record_refresh(1);       /* a full update by definition */
    /* Start the datasheet's 24 h clock here too. This IS a full refresh of the panel, so it is the
     * moment the clock restarts; leaving it at 0 would make the first tick's hours_since_full()
     * read 0 and postpone the ghosting-clearing refresh by however long this image stayed up. */
    s_last_full_us = esp_timer_get_time();
    ESP_LOGI(TAG, "last-good image pushed (slot %d)", slot);
    return ESP_OK;
}

/* The credentials every fetch needs, read once from NVS. Sizes come from nvs_keys.h so the
 * reader and the writers cannot disagree about how long a value may be. */
typedef struct {
    char   key[DEVENV_BUF_OWM_KEY];
    double lat, lon;
    char   ha_url[DEVENV_BUF_HA_URL];
    char   ha_token[DEVENV_BUF_HA_TOKEN];
} fetch_creds_t;

static int read_creds(fetch_creds_t *c)
{
    memset(c, 0, sizeof(*c));
    nvs_handle_t h;
    if (nvs_open(DEVENV_NVS_NAMESPACE, NVS_READONLY, &h) != ESP_OK) return -1;
    size_t n = sizeof(c->key);
    nvs_get_str(h, DEVENV_KEY_OWM_KEY, c->key, &n);
    /* A missing location is not fatal: 0,0 is a defined place (the Gulf of Guinea) and the
     * resulting reading is obviously wrong, which is better than no reading and a silent
     * failure. */
    size_t llen = sizeof(double);
    nvs_get_blob(h, DEVENV_KEY_LOC_LAT, &c->lat, &llen);
    llen = sizeof(double);
    nvs_get_blob(h, DEVENV_KEY_LOC_LON, &c->lon, &llen);
    n = sizeof(c->ha_url);
    const esp_err_t e_url = nvs_get_str(h, DEVENV_KEY_HA_URL, c->ha_url, &n);
    n = sizeof(c->ha_token);
    const esp_err_t e_tok = nvs_get_str(h, DEVENV_KEY_HA_TOKEN, c->ha_token, &n);
    nvs_close(h);

    /* NORMALISE THE URL ON READ, not only on write. fetch_ha() appends "/api/template", so a
     * trailing slash here becomes a double slash — a 404 on some HA reverse proxies that reads
     * like a bad token. PUT /api/secrets strips it, but the captive portal does not, and a device
     * provisioned there could have one stored from before this rule existed. Normalising at the
     * point of use makes every stored form work, including values already in flash that no write
     * path will revisit. A URL that fails to normalise is left as-is: the fetch will fail and log,
     * which is the pre-existing behaviour for a malformed address. */
    if (c->ha_url[0]) {
        char norm[DEVENV_BUF_HA_URL];
        if (devcfg_normalize_ha_url(c->ha_url, norm, sizeof(norm)) == 0) {
            snprintf(c->ha_url, sizeof(c->ha_url), "%s", norm);
        }
    }

    /* LOG A TRUNCATED/FILTERED READ rather than leaving a zeroed field that reads as "not
     * configured". nvs_get_str returns ESP_ERR_NVS_INVALID_LENGTH when the stored value does not
     * fit, and a caller that ignores it turns a stored credential into a silently absent one —
     * the exact failure a mismatched buffer size caused. The buffer sizes are now shared, so this
     * should not fire; it is here because the symptom is otherwise indistinguishable from an
     * unconfigured device. */
    if (e_url == ESP_ERR_NVS_INVALID_LENGTH)
        ESP_LOGW(TAG, "stored HA url is longer than %d bytes; ignoring it", DEVENV_BUF_HA_URL);
    if (e_tok == ESP_ERR_NVS_INVALID_LENGTH)
        ESP_LOGW(TAG, "stored HA token is longer than %d bytes; ignoring it", DEVENV_BUF_HA_TOKEN);
    return 0;
}

/* The forecast horizon, and the buffer that must hold the response. THE TWO ARE DEFINED TOGETHER
 * ON PURPOSE — see the note on the size below.
 *
 * OWM takes `cnt` as a count of 3-hour blocks, 8 per day, and the layout's highest `dayIndex`
 * says how many days are needed. 40 blocks is the whole 5-day horizon the free 2.5/forecast
 * product carries; asking for more returns the same data with a misleading count. */
#define FORECAST_MAX_BLOCKS OWM_FORECAST_MAX_BLOCKS

/* The forecast document buffer, and its size is a MEMORY constraint rather than a taste choice.
 *
 * MEASURED FAILURE THIS SIZING FIXES: a full 5-day/3-hour response is 16,575 bytes, and holding a
 * 20 KB buffer for it while the TLS handshake ALSO needs a contiguous in-buffer on this part made
 * the handshake fail with `mbedtls_ssl_setup returned -0x7F00` (ALLOC_FAILED) — observed as
 * "forecast request failed" and `--` in every forecast box, with a largest-free-block of only
 * 30,720 bytes at that moment. The device was competing with itself.
 *
 * So the request is bounded to the days the layout actually asks for — but the bound and this
 * buffer MUST AGREE, and they did not. The request was allowed up to cnt=40 while this was 12,288
 * bytes, and the response grows ~406 bytes per block (measured live 2026-09-20: 3,512 at cnt=8,
 * 6,819 at 16, 10,069 at 24, 13,314 at 32, 16,575 at 40). net_http refuses to hand a parser a
 * clipped document and reports ESP_ERR_NO_MEM, so every request past 3 days failed outright and
 * EVERY forecast widget fell back to "--" — while the web app happily offers Day 4 and Day 5 in
 * its day picker. The failure was invisible in the config and silent on the glass.
 *
 * The size now comes from owm_forecast_buf_bytes(), which is host-tested (test/test_owm_parse):
 * the request and the buffer are derived from one rule, so they cannot drift apart again. The
 * 17 KB this works out to is affordable because the request happens BEFORE the render window,
 * while the resident framebuffer is released on USB — the same window the old 12,288 fit in. */
#define FORECAST_BUF_BYTES ((size_t)owm_forecast_buf_bytes(FORECAST_MAX_BLOCKS))

/* ---- The split interval: is OWM due this tick? --------------------------------------------
 *
 * `owm_seconds` is the OWM cadence (>= the tick interval, see layout_config_t). The FIRST tick
 * after boot is always due (no timestamp yet), and every tick is due when the two intervals are
 * equal — which is the default and every pre-split config, so this adds no behaviour change there.
 *
 * `s_last_owm_fetch_us` is esp_timer time, so it resets on every boot: on battery each wake is a
 * fresh boot and therefore always due, which is correct — there is one refresh per wake and a
 * retained document could not survive esp_deep_sleep_start() anyway. The split is a mains behaviour. */
static int owm_fetch_due(int owm_seconds)
{
    if (owm_seconds <= 0) return 1;
    if (s_last_owm_fetch_us == 0) return 1;
    const int64_t elapsed_ms = (esp_timer_get_time() - s_last_owm_fetch_us) / 1000;
    return elapsed_ms >= (int64_t)owm_seconds * 1000;
}

/* Make the retained forecast buffer hold at least `need` bytes.
 *
 * SIZED TO WHAT THE LAYOUT ASKED FOR, not to the 40-block maximum: the request is already bounded
 * to the days the page binds (see fetch_forecast), so for a typical today+tomorrow layout the
 * answer is ~6.8 KB rather than the 17.3 KB the full horizon needs — and on this part every
 * resident byte is contiguous DRAM the render window does not get. Only when the page binds
 * further-out days does this grow. A cache already large enough is kept as-is; it only grows.
 *
 * THIS IS SAFE TO HOLD RESIDENT because the tick releases the 78,200-byte static layer before it
 * fetches (see the release note at the top of refresh_tick_locked), so the TLS handshake sees the
 * big region minus these few KB, not minus the layer. The cost lands on the RENDER window's band
 * buffers instead, which retry at a smaller size when the block is tight (see push_banded). */
static int ensure_forecast_cache(size_t need)
{
    if (need == 0) need = FORECAST_BUF_BYTES;
    if (s_forecast_cache && s_forecast_cap >= need) return 0;

    char *next = heap_caps_malloc(need, MALLOC_CAP_8BIT);
    if (!next) {
        ESP_LOGW(TAG, "no heap for the retained forecast cache (%u bytes); "
                      "OWM will re-fetch every tick instead", (unsigned)need);
        return -1;
    }
    free(s_forecast_cache);
    s_forecast_cache = next;
    s_forecast_cap = need;
    s_have_forecast_cache = 0;      /* fresh buffer holds no document yet */
    return 0;
}

/* Drop the retained forecast document. Called when a config change turns the split off, so the
 * resident bytes are given back rather than held for a feature no longer in use. */
static void forecast_cache_release(void)
{
    free(s_forecast_cache);
    s_forecast_cache = NULL;
    s_forecast_cap = 0;
    s_have_forecast_cache = 0;
}

/* Whether this device's key has One Call 3.0 available, once probed.
 *
 * TRI-STATE, and all three values are load-bearing:
 *   -1  not probed yet, or the probe could not reach a verdict
 *    0  probed: the key is definitively not subscribed (the documented 401/403)
 *    1  probed: One Call 3.0 answered
 *
 * Cached for the process lifetime because the answer is a property of the KEY, not of the
 * request: re-probing on every refresh would spend a call on a request that is already known to
 * fail, and on a 10-minute cadence that is 144 wasted calls a day against a quota FR-6a exists
 * to protect. */
static int s_onecall_available = -1;

/* Fetch the current conditions from OWM. Returns 0 on success, -1 otherwise.
 *
 * `product` decides the ENDPOINT, which is what makes the config toggle real (FR-6). One Call
 * 3.0 carries current conditions inside its single document, so on that product the forecast
 * fetch below is the one that supplies them and this returns "nothing to do" — asking
 * 2.5/weather as well would be a second call for data already held, against a quota. */
static int fetch_current(const fetch_creds_t *c, char *resp, size_t resplen,
                         datasrc_value_t *out, owm_product_t product)
{
    if (c->key[0] == '\0') {
        ESP_LOGW(TAG, "no OWM key stored; skipping fetch");
        return -1;
    }

    /* One Call 3.0 has no separate current-conditions endpoint: everything rides in the one
     * document, which fetch_forecast() requests. Composing this into the SAME buffer would mean
     * a second ~11 KB response held in the render window for no new data. */
    if (product == OWM_PRODUCT_ONECALL3) {
        memset(out, 0, sizeof(*out));
        out->status = DATASRC_ERR_UNAVAILABLE;
        return 0;
    }

    /* The daily cap is checked BEFORE the request, which is the only point at which it can
     * actually prevent a call (spec §3.4). Reaching it means roughly 7x the expected call
     * rate has occurred, so this fires only on a runaway refresh — the panel keeps its last
     * good image and the error is recorded for /api/status, where the count is also visible. */
    if (!api_owm_should_call()) {
        ESP_LOGE(TAG, "OWM daily call cap reached; not fetching (see /api/status)");
        api_note_error("owm: daily call cap reached");
        return -1;
    }

    /* `units=imperial` is REQUIRED, not cosmetic (spec §3.4). Without it OWM returns the
     * default — Kelvin — and the panel silently shows 288.4 where the user expects 59.0. The
     * failure is quiet because a Kelvin reading is still a plausible-looking number, so
     * nothing errors; it simply disagrees with the user's Home Assistant entities, which is
     * the comparison they will make. The spec settles it: `imperial` gives °F and mph and
     * matches those entities. */
    char url[512];
    snprintf(url, sizeof(url),
             "https://api.openweathermap.org/data/2.5/weather"
             "?lat=%.6f&lon=%.6f&units=imperial&appid=%s", c->lat, c->lon, c->key);

    if (net_http_get_json(url, NULL, resp, resplen) != ESP_OK) {
        ESP_LOGW(TAG, "OWM request failed");
        return -1;
    }

    /* Still parsed for its own timestamp, so the daily call cap is credited to the day the
     * response belongs to. A failed request carries no timestamp, so observed_at stays 0 and
     * api_owm_note_call() ignores it: a failed request still costs a call, but crediting it to
     * the wrong day would be worse than undercounting. */
    *out = owm_parse_current_temp(resp, (long)(esp_timer_get_time() / 1000000LL));
    api_owm_note_call(out->observed_at, 1);

    return out->status == DATASRC_OK ? 0 : -1;
}

/* FR-6's One Call 3.0 probe, run once per process.
 *
 * WHY A PROBE RATHER THAN A CONFIG GUESS: One Call 3.0 needs the separate "One Call by Call"
 * subscription, and a key without it gets a 401. Verified live 2026-09-18 with this project's
 * key: 3.0 -> 401 "requires a separate subscription", 2.5/weather and 2.5/forecast -> 200. So
 * "does this key have 3.0" is not knowable from the config, and FR-6 asks for exactly this
 * auto-detection.
 *
 * THE VERDICT IS THE HTTP STATUS, NOT THE RESPONSE BODY — and that distinction is the whole
 * correctness of this function. An earlier version sized the scratch buffer at 2 KB and treated
 * ANY failure as "not subscribed". The trimmed One Call document is ~11 KB, so the buffer always
 * overflowed (net_http returns ESP_ERR_NO_MEM, deliberately, rather than handing a parser a
 * clipped document), and a key that IS subscribed was reported as unsubscribed. The consequence
 * was not confined to a log line: FR-7 then told the user on the glass that official alerts were
 * unavailable on their product, on a key that had them. So the probe now asks for the status and
 * only the documented 401/403 counts as a definite "no".
 *
 * It is a real request, and it costs a call — which is why the answer is cached: the probe runs
 * ONCE, and on a key without the subscription every later refresh goes straight to 2.5 instead
 * of paying for another 401. The cap is charged for it, because it is a call.
 *
 * Returns 1 available, 0 definitively not subscribed, -1 inconclusive (leave the question open
 * and fall back to the free pair for now). */
static int onecall_probe(const fetch_creds_t *c)
{
    if (s_onecall_available >= 0) return s_onecall_available;
    if (c->key[0] == '\0') return -1;           /* nothing to probe with */
    if (!api_owm_should_call()) return -1;      /* do not spend a call we are not allowed */

    char url[512];
    snprintf(url, sizeof(url),
             "https://api.openweathermap.org/data/3.0/onecall"
             "?lat=%.6f&lon=%.6f&exclude=minutely,hourly,current,daily&units=imperial&appid=%s",
             c->lat, c->lon, c->key);

    /* The body is DISCARDED — only the status decides — so this buffer is deliberately tiny. It
     * is not "big enough for the response" and must not be read as if it were: `exclude` trims
     * the document, but even the alerts-only remainder exceeds 2 KB on a real key, so the request
     * is EXPECTED to report overflow. That is fine here precisely because the status is still
     * reported: esp_http_client_perform() completes and the status is read before the sink's
     * overflow flag is consulted, so a 200 with a clipped body still proves the key is
     * subscribed. A 2 KB static scratch also keeps a ~11 KB transient out of the render window,
     * where it would compete with the 78,200-byte framebuffer. */
    static char probe[2048];
    int status = 0;
    const esp_err_t e = net_http_get_json_status(url, NULL, probe, sizeof(probe), &status);

    if (status == 200) {
        s_onecall_available = 1;
        ESP_LOGI(TAG, "One Call 3.0 is available for this key");
    } else if (status == 401 || status == 403) {
        /* The documented answer for a key without the "One Call by Call" subscription. This is
         * the NORMAL path, not an error worth surfacing. */
        s_onecall_available = 0;
        ESP_LOGI(TAG, "One Call 3.0 not available (no subscription); using the free 2.5 products");
    } else {
        /* Anything else — a transport failure, a 5xx, a DNS problem — says nothing about the
         * subscription, so the question is left OPEN and the free pair is used meanwhile. Latching
         * a 0 here would permanently downgrade a subscribed key on one flaky request. */
        ESP_LOGW(TAG, "One Call probe inconclusive (status %d, %s); staying on the free products",
                 status, esp_err_to_name(e));
        return -1;
    }
    api_owm_note_call(0, 1);        /* a real call, credited to no particular day */
    return s_onecall_available;
}

/* Fetch the forecast into `buf`. Returns 0 on success.
 *
 * `days` is how many days the layout's widgets actually reference, taken from the highest
 * dayIndex they bind. The request is bounded with OWM's `cnt` (3-hour blocks, 8 per day) rather
 * than asking for the full 5-day document and discarding most of it: the full response is
 * 16,522 bytes measured, and carrying that much live while the TLS handshake needs ~20 KB
 * contiguous made the handshake fail with ALLOC_FAILED (see FORECAST_BUF_BYTES).
 *
 * A `days` of 0 means "ask for the whole horizon", which is what an alert-only page wants: the
 * official alerts ride in this document, so the page needs it fetched but not trimmed.
 *
 * `product` selects the ENDPOINT (FR-6). On One Call 3.0 there is no separate forecast product:
 * this ONE document carries current conditions, the daily array, and the official alerts, which
 * is why the tick treats it as the current document too when that product is active. */
static int fetch_forecast(const fetch_creds_t *c, char *buf, size_t buflen, int days,
                          owm_product_t product)
{
    if (c->key[0] == '\0') return -1;
    if (!api_owm_should_call()) {
        api_note_error("owm: daily call cap reached");
        return -1;
    }

    char url[512];
    if (product == OWM_PRODUCT_ONECALL3) {
        /* `minutely` and `hourly` are excluded because no widget binds them and together they
         * dominate the document (~11 KB of the ~16 KB). `current` and `daily` are KEPT: the
         * current conditions and the daily min/max are exactly what the page draws, and `alerts`
         * cannot be excluded without defeating FR-7. */
        snprintf(url, sizeof(url),
                 "https://api.openweathermap.org/data/3.0/onecall"
                 "?lat=%.6f&lon=%.6f&exclude=minutely,hourly&units=imperial&appid=%s",
                 c->lat, c->lon, c->key);
    } else if (days > 0) {
        /* Clamped to the 5-day horizon the free product carries. The clamp and FORECAST_BUF_BYTES
         * are both derived from FORECAST_MAX_BLOCKS so the request can never outgrow the buffer
         * that receives it — the mismatch that made every Day 4/5 widget render "--". */
        int cnt = days * 8;
        if (cnt > FORECAST_MAX_BLOCKS) cnt = FORECAST_MAX_BLOCKS;
        snprintf(url, sizeof(url),
                 "https://api.openweathermap.org/data/2.5/forecast"
                 "?lat=%.6f&lon=%.6f&units=imperial&cnt=%d&appid=%s",
                 c->lat, c->lon, cnt, c->key);
    } else {
        snprintf(url, sizeof(url),
                 "https://api.openweathermap.org/data/2.5/forecast"
                 "?lat=%.6f&lon=%.6f&units=imperial&appid=%s", c->lat, c->lon, c->key);
    }

    if (net_http_get_json(url, NULL, buf, buflen) != ESP_OK) {
        ESP_LOGW(TAG, "%s request failed",
                 product == OWM_PRODUCT_ONECALL3 ? "onecall" : "forecast");
        return -1;
    }
    /* Credit the call against today, taken from the response's own first timestamp. The two
     * products carry it in different places ("list"[0]."dt" for 2.5/forecast, the top-level "dt"
     * for One Call), and a response with neither is not a forecast, so it is not credited to a
     * day that might be wrong. */
    cJSON *root = cJSON_Parse(buf);
    if (root) {
        cJSON *dt = cJSON_GetObjectItemCaseSensitive(
                        cJSON_GetArrayItem(cJSON_GetObjectItemCaseSensitive(root, "list"), 0), "dt");
        if (!cJSON_IsNumber(dt)) dt = cJSON_GetObjectItemCaseSensitive(root, "dt");
        api_owm_note_call(cJSON_IsNumber(dt) ? (long)dt->valuedouble : 0, 1);
        cJSON_Delete(root);
    }
    return 0;
}

/* Fetch the page's Home Assistant entities in ONE template call (FR-5a).
 *
 * THE KEY OPTIMISATION: HA renders a template server-side, so the device sends one small POST
 * naming exactly the entities the layout needs and receives one small '|'-separated line
 * ("68.4|41.2"). N per-entity GETs would be N round trips, and /api/states returns every entity
 * on the instance — far too large for a 320 KB part with no PSRAM. */
static int fetch_ha(const fetch_creds_t *c, char (*ids)[48], int n_ids,
                    char *out, size_t outlen)
{
    if (n_ids <= 0) return 0;               /* nothing bound: no request to make */
    if (c->ha_url[0] == '\0' || c->ha_token[0] == '\0') {
        ESP_LOGW(TAG, "HA entities are bound but no HA url/token is stored");
        return -1;
    }

    /* Build the template body: {"template": "{{ states('a') }}|{{ states('b') }}"}.
     * ha_template_add_entity() validates each id against HA's grammar, which matters because an
     * unvalidated id would be interpolated into a Jinja template — a quote in an entity id would
     * be template injection, not merely a bad request. */
    char tmpl[600];
    int len = 0;
    for (int i = 0; i < n_ids; i++) {
        const int next = ha_template_add_entity(tmpl, (int)sizeof(tmpl), len, ids[i]);
        if (next < 0) {
            ESP_LOGW(TAG, "entity template overflow at %d entities", i);
            break;
        }
        len = next;
    }
    if (len == 0) return -1;

    char body[700];
    const int n = snprintf(body, sizeof(body), "{\"template\":\"%s\"}", tmpl);
    if (n < 0 || (size_t)n >= sizeof(body)) return -1;

    char url[256];
    snprintf(url, sizeof(url), "%s/api/template", c->ha_url);

    if (net_http_post_json(url, c->ha_token, body, out, outlen) != ESP_OK) {
        ESP_LOGW(TAG, "HA template request failed");
        return -1;
    }
    return 0;
}

/* Return the layer's DRAM to the heap, WITH the lock already held. Memory only — it does NOT
 * touch the glass-identity flags, because those describe what is ON THE GLASS, which freeing
 * RAM does not change. See release_glass_locked() for the callers that must also forget the
 * picture. Defined here rather than beside layer_lock() because it frees s_static_contig, which
 * is declared with the setup-screen code below. */
static void free_layer_locked(void)
{
    segbuf_free(&s_layer, layer_seg_free);
    artwork_inflate_release(s_inflate); s_inflate = NULL;
    free(s_static_contig); s_static_contig = NULL;
}

/* Forget which picture is on the glass, so the next push must be a FULL refresh.
 *
 * WHY A PARTIAL WOULD BE WRONG AFTERWARDS: a partial diffs the new frame against the previous
 * one, which is REPRODUCED from the layer plus the recorded values. Once either is gone, the
 * firmware cannot rebuild the frame that is actually up there, so it would diff against a frame
 * that was never displayed and leave ghosted fragments. Clearing BOTH the identity and the
 * presence flag is what makes refresh_decide() see "nothing on the glass" and choose a full. */
static void release_glass_locked(void)
{
    free_layer_locked();
    s_shown_slot = SLOT_NONE;
    s_glass_present = 0;
    s_have_prev_values = 0;
}

esp_err_t app_fbs_reserve(void)
{
    esp_err_t r;
    layer_lock();
    /* ONE buffer, and it holds the static layer. An earlier version reserved TWO 78,200-byte
     * framebuffers here, which starved the radio: measured, the device had 2.9 KiB left after the
     * two framebuffers, the linker's static DRAM and esp_wifi_init(), so the driver aborted with
     * ESP_ERR_NO_MEM and the device could not be provisioned. The band buffers the push needs are
     * acquired inside the render window and are two orders of magnitude smaller (see push_banded). */
    r = ensure_static() == 0 ? ESP_OK : ESP_ERR_NO_MEM;
    layer_unlock();
    return r;
}

void app_fbs_release(void)
{
    layer_lock();
    release_glass_locked();
    layer_unlock();
    ESP_LOGI(TAG, "static layer released (%u bytes back to the heap)", (unsigned)EPD_FB_BYTES);
}

int app_fetch_pause(void)
{
    /* Take the layer away from the render path for the duration of a fetch on THIS task (the
     * httpd task, normally). Waiting for the lock means a tick already in flight finishes first,
     * and the tick's own acquisition of the same lock (below) means no render starts while the
     * layer is gone.
     *
     * MEMORY ONLY — the glass-identity flags are deliberately left alone. The fetch does not
     * change what is on the panel, and the layer is reproducible from flash, so the next tick
     * reloads it and can still take FR-11's partial rather than being forced into a full flash
     * for a check that may well have found nothing newer. */
    layer_lock();
    const int had = (s_layer.n > 0) || s_static_contig != NULL;
    free_layer_locked();
    if (had) {
        ESP_LOGI(TAG, "static layer released for an out-of-band fetch (%u bytes)",
                 (unsigned)EPD_FB_BYTES);
    }
    return had;
}

void app_fetch_resume(void)
{
    layer_unlock();
}

/* Draw the "how to set this up" screen: the AP name, the BLE PoP, and QR codes for the setup
 * page and the two provisioning apps (FR-30).
 *
 * Uses the resident static layer, because this runs at the last moment before provisioning needs
 * the memory back — so it must not ask for a second 78,200-byte buffer it is about to hand over.
 * Overwriting the layer is safe and deliberate: the boot path releases it immediately afterwards,
 * and the identity is cleared so the next render reloads a real one rather than diffing a partial
 * against the setup screen. Composed via lib/provscreen, which is host-tested (the QR modules are
 * verified byte-for-byte against the reference matrices; see test/test_provscreen). */
void app_render_setup_screen(void)
{
    /* Give the segmented render layer back FIRST. The setup screen needs a whole contiguous frame
     * for epd_write_frame(), and holding both at once is 156 KB — more than the boot heap has.
     * Nothing needs the segmented layer after this point: the boot path releases all of it
     * immediately afterwards, and this screen clears the glass identity anyway. */
    segbuf_free(&s_layer, layer_seg_free);
    artwork_inflate_release(s_inflate); s_inflate = NULL;

    if (ensure_static_contiguous() != 0) {
        ESP_LOGE(TAG, "cannot draw the setup screen: no contiguous static layer");
        return;
    }

    char ap_ssid[32];
    prov_service_name(ap_ssid, sizeof(ap_ssid));

    /* Pass the brand badge in HERE rather than drawing it first: the render fills the page
     * white before composing, so anything drawn beforehand would be erased. */
    if (provscreen_render_branded(s_static_contig, ap_ssid, PROV_POP_STRING,
                                  boot_badge, boot_badge_w, boot_badge_h) != 0) {
        ESP_LOGE(TAG, "setup screen render failed");
        return;
    }

    if (epd_wake() != ESP_OK) {
        ESP_LOGE(TAG, "panel did not wake for the setup screen");
        return;
    }

    /* Pushed whole rather than banded: the renderer above already produced the full frame in the
     * layer buffer, so a band pass would only re-read it a band at a time for no memory saving. */
    const esp_err_t e = epd_write_frame(s_static_contig);
    if (e == ESP_OK) {
        /* Identity cleared, NOT set: this is not the layout bitmap and it carries no layout
         * values, so marking it otherwise would authorise a later partial to diff a real layout
         * against the setup screen. Presence is cleared with it for the same reason — something IS
         * on the glass, but it is not something this firmware can reproduce, and a full refresh is
         * the only correct way to replace it. */
        s_shown_slot = SLOT_NONE;
        s_glass_present = 0;
        s_have_prev_values = 0;
        ESP_LOGI(TAG, "setup screen shown: SSID \"%s\"", ap_ssid);
    } else {
        ESP_LOGE(TAG, "setup screen push failed: %s", esp_err_to_name(e));
    }
    epd_sleep();
}

/* ---------------------------------------------------------------------------------------
 * WHY THE BAND BUFFERS ARE TRANSIENT RATHER THAN RESIDENT
 *
 * Measured on this part: total DRAM available for dynamic allocation is 234.2 KiB, and
 * esp_wifi_init() alone takes 26.2 KiB (5 static RX buffers, a 6.6 KiB driver task, the
 * management and dynamic pools). Add the linker's 52.4 KiB of static .bss/.data and two
 * 76.4 KiB framebuffers and the sum is 312 KiB against 234 available — the device cannot hold
 * TWO FRAMEBUFFERS and a live radio at the same time. With two reserved up front,
 * esp_wifi_init() failed with ESP_ERR_NO_MEM ("Expected to init 10 rx buffer, actual is 6")
 * and the HTTP server then failed with ESP_ERR_HTTPD_ALLOC_MEM, leaving the device with a
 * working panel and no way to configure it. Only ~2.9 KiB was left.
 *
 * Only ONE whole-panel buffer is needed for any length of time: the static layer, because it is
 * the expensive half (78,200 bytes) and both frames of a partial are derived from it. The band
 * buffers the push composes into are 31 KB for the pair together — small enough to be taken and
 * given back inside the render window, and the reason a partial is possible here at all.
 *
 * The panel is bistable and is put to sleep after every push, so releasing them costs nothing
 * visually — the image is on the glass, not in RAM.
 * ------------------------------------------------------------------------------------- */

/* The tick body, run with the layer lock held. Split from app_refresh_tick() so the lock is
 * taken and given back in ONE place: this function has many early returns (a failed layer
 * acquire, a panel that will not wake, a thermal block, a failed push), and releasing the lock
 * on each of them by hand is exactly the kind of bookkeeping that rots. */
static void refresh_tick_locked(power_source_t source, int force_full)
{
    /* The render window's heap profile, printed at the four points that bracket it. With
     * HEAP_TRACE unset these expand to nothing (see heap_trace.h) — they exist so a bench round
     * can see WHERE the contiguous block goes without re-instrumenting and re-flashing. */
    HEAP_DIAG("tick entry");

    /* The static layer is NOT acquired here, on either power source.
     *
     * It used to be held across the fetch, so the frame would survive as the diff base for a
     * partial refresh. That is no longer possible or useful: the fetch needs the region far more
     * than the layer does (see the release below), and on battery a partial was never reachable
     * anyway — one refresh per wake, then deep sleep, with the layer and its values living in RAM
     * that does not survive esp_deep_sleep_start().
     *
     * Acquiring it here would also be actively HARMFUL. When the re-acquire at the END of a tick
     * fails on a fragmented region, s_layer is left empty; an entry acquire would then fail too and
     * the tick would return BEFORE the fetch, so one failed render costs the NEXT tick's data as
     * well as its image, and the device stays stale for several ticks while the region clears
     * (measured: one failure cascaded into four). Not acquiring means a failed render costs only
     * that tick's image; the next tick fetches and draws normally.
     *
     * The layer is taken once, at the re-acquire below, after the radio is down and the fetch
     * buffers are freed — which is the point at which it is actually needed and most likely to fit.
     *
     * THE RE-ACQUIRE IS NOW RELIABLE WHERE IT USED TO RACE: the layer is held as SEGMENTS, so it no
     * longer needs the ONE contiguous 78,200-byte block that the live API fragments below size. See
     * ensure_static(). */
    /* The SAME release app_fetch_pause() uses, so "the layer is not resident" has one definition.
     * The identity flags are deliberately NOT cleared here (see the note below), which is why this
     * cannot simply call app_fbs_release(). */
    segbuf_free(&s_layer, layer_seg_free);
    /* The strip decoder is released at tick entry too, so a tick that failed after reserving it
     * cannot carry the ~11 KB into the next tick's fetch. It is re-reserved by ensure_static(). */
    artwork_inflate_release(s_inflate); s_inflate = NULL;
    HEAP_DIAG("tick entry (no static layer held)");
    /* ---- THE STATIC LAYER IS RELEASED ACROSS THE FETCH, ON BOTH POWER SOURCES ----
     *
     * WHY IT MUST BE: the TLS handshake needs CONTIGUOUS DRAM for the in-buffer, the out-buffer,
     * the X.509 verification working set and the worker's own stack, and it can only come from the
     * ONE region large enough for a 78,200-byte buffer (measured: region 0x3ffe4350, 113,840 bytes —
     * every other region caps at 64,936). Holding the layer there leaves 35,640 bytes for
     * everything else, which is not enough. Measured, holding it makes EVERY fetch fail:
     * `mbedtls_ssl_setup returned -0x7F00` (ALLOC_FAILED) and `PK verify failed` (X509 alloc),
     * with every reading falling back to "--".
     *
     * THIS APPLIES ON BATTERY TOO, and the earlier "on battery the layer is held and both fit"
     * reasoning was WRONG — it was true only while the TLS in-buffer was 8192. At the 16384 the
     * server's TLS records actually require (see sdkconfig.defaults), the arithmetic is
     * 78,200 (layer) + 16,384 (TLS in) + ~4 K (out) + ~19 K (forecast) > 113,840. Measured on the
     * bench in battery mode: the handshake failed for BOTH fetches and the panel drew placeholders.
     * The fetch buffers and the layer cannot coexist in that region at any tolerable buffer size.
     *
     * RELEASING COSTS NOTHING ON BATTERY EITHER, because a partial refresh there was never
     * possible in the first place: the device performs ONE refresh per wake and then deep-sleeps,
     * and s_layer / s_prev_values / s_shown_slot live in ordinary RAM that does not survive
     * esp_deep_sleep_start(). So there is no diff base to preserve across a fetch — every battery
     * render is necessarily a full refresh, and the 78,200 bytes are better spent on the fetch.
     * FR-11's partial strategy belongs to the always-on path, where it is what keeps flicker and
     * refresh time down.
     *
     * The cost of releasing is the re-acquire below, which can fail while the region is
     * fragmented — see ensure_static()'s bounded wait, which is what makes that re-acquire reliable.
     * The panel is bistable and asleep between pushes, so releasing costs nothing visible. */

    /* NOTE: s_shown_slot and s_glass_present are deliberately NOT cleared here. They describe the
     * picture ON THE GLASS, which releasing the RAM does not change — the frame is still up there.
     * Clearing them would say "nothing on the glass" and force a FULL refresh on every tick, which
     * is how an earlier version of this function made FR-11's partial path dead code. They are
     * cleared only when the glass is genuinely overwritten by something unreproducible or the layer
     * is dropped — app_fbs_release() and the setup screen. */

    /* WiFi credentials live in NVS, written by provisioning (FR-30) — never compiled in.
     * net_wifi_connect() needs them explicitly, so they are read here rather than assumed. */
    char ssid[64] = {0};
    char pass[128] = {0};
    size_t slen = sizeof(ssid), plen = sizeof(pass);
    nvs_handle_t h;
    if (nvs_open(DEVENV_NVS_NAMESPACE, NVS_READONLY, &h) == ESP_OK) {
        nvs_get_str(h, DEVENV_KEY_WIFI_SSID, ssid, &slen);
        nvs_get_str(h, DEVENV_KEY_WIFI_PASS, pass, &plen);
        nvs_close(h);
    }

    if (ssid[0] == '\0') {
        /* Unprovisioned is a NORMAL first-boot state, not an error: the device has no
         * credentials yet and is waiting to be set up. The last good image stays up and the
         * device stays reachable over the API so it CAN be set up. */
        ESP_LOGI(TAG, "no WiFi credentials stored; waiting to be provisioned");
        return;
    }

    /* Connect with a bounded wait. A failure here is not fatal — the last good image stays
     * up and the device stays reachable (FR-29). */
    esp_err_t e = net_wifi_connect(ssid, pass, 20000);
    if (e != ESP_OK) {
        ESP_LOGW(TAG, "no network (%s); keeping the last good image", esp_err_to_name(e));
        api_note_error("net: connect failed");
        return;
    }

    /* Fill in a city-level location from the public IP, but ONLY if the user has not set one
     * (FR-30). This runs on the first refresh after a device joins a network it was just
     * provisioned for, so the config page the user opens next already has plausible
     * coordinates in its fields instead of two empty boxes they would have to fill from a
     * map. It is a DEFAULT, never an overwrite — see geo_ip.c for why that distinction is the
     * whole point. Cheap on every later boot: one NVS read, no request. */
    if (geo_ip_fill_if_unset()) {
        ESP_LOGI(TAG, "location was empty; filled it from the public IP (a city-level guess)");
    }

    /* 4 KB, and the size is load-bearing rather than arbitrary.
     *
     * This is static, so it lives in .bss — and on this part .bss ends exactly where the
     * second-largest DRAM heap region begins, so every byte here is a byte that region does
     * not have. The panel needs TWO contiguous 78,200-byte framebuffers, one of which must
     * come from that region, and it can only satisfy a request that fits a TLSF size class
     * (multiples of 4 KB at this size). At 8 KB this buffer pushed the region's largest
     * satisfiable block down to 77,824 — 376 bytes short of a framebuffer — and the device
     * booted unable to draw anything at all. See app_fbs_reserve().
     *
     * 4 KB is still ~8x the current-weather response: OWM 2.5/weather for a full document with
     * a long place name measures ~521 bytes. The FORECAST document does NOT fit here and is not
     * asked to — it is ~16.5 KB and gets a transient heap buffer instead (see
     * FORECAST_BUF_BYTES), because growing this array is exactly what starved the framebuffer. */
    static char resp[4096];

    /* ---- What does this page actually need? ----
     *
     * Resolved BEFORE fetching so that one forecast document serves every forecast widget, and
     * a page with no Home Assistant binding makes no HA request at all. */
    layout_config_t cfg;
    memset(&cfg, 0, sizeof(cfg));
    /* ONE read of the stored document, used for BOTH the config and the page's widgets.
     *
     * Reading it twice (once for the config, once for the widgets) is not merely wasteful: each
     * read allocates the full CFG_JSON_MAX_LEN block, and on USB these reads happen in the window
     * between releasing the resident framebuffer for the fetch and re-acquiring it for the render.
     * A transient block that big lands inside the freshly-freed 78 KB hole and splits it, which is
     * exactly the fragmentation that can make the re-acquire fail. One read, one free. */
    char *cfg_json = NULL;
    int cfg_ok = (cfg_store_get(cfg_store_nvs(), &cfg_json) == 0 && cfg_json != NULL);
    if (cfg_ok && layout_config_parse(cfg_json, &cfg) != 0) cfg_ok = 0;
    if (!cfg_ok) {
        ESP_LOGW(TAG, "stored config unparseable; using defaults");
        cfg.update_seconds = 900;
        cfg.owm_update_seconds = 900;
        cfg.partial_refresh_limit = 5;
        cfg.page_count = 1;
    }

    /* WHICH PAGE: the rotation schedule, from real elapsed time since boot. FR-15 wants the
     * device to cycle pages on its own, and this is the only place that can happen.
     *
     * AN EXPLICIT OVERRIDE WINS FOR ONE FRAME: the layout editor asks for the page it is editing
     * so a change to a non-scheduled page shows within a second instead of after that page's
     * rotation slot (fifteen minutes with the shipped intervals). The request is NOT consumed here
     * — it is cleared only after a frame carrying it is actually pushed (api_clear_page() at the
     * end), so a tick that fails to get its framebuffer and draws nothing does not silently drop
     * the user's request. It is clamped to a page this config actually has — a stale request from
     * a deleted page must not index past the array. */
    const long elapsed_s = (long)(esp_timer_get_time() / 1000000LL);
    int page_index = layout_page_at(&cfg, elapsed_s);
    const int page_want = api_take_page();
    int page_forced = 0;
    if (page_want >= 0) {
        if (page_want < cfg.page_count) {
            page_index = page_want;
            page_forced = 1;
        } else if (cfg_ok) {
            /* The config is known good and has no such page, so this request can never be
             * honoured. DISCARD it rather than leaving a stale index pending: if the user later
             * adds pages, a request that silently took effect then would be a page change nobody
             * asked for at that moment. When the config could NOT be parsed the request is kept,
             * because the page count is then a default and the request may still be valid. */
            api_clear_page(page_want);
        }
    }

    static page_render_t page;      /* static: ~4 KB of widgets, too big for the 3.5 KB stack */
    memset(&page, 0, sizeof(page));

    /* WHAT THE WHOLE DOCUMENT NEEDS, not just the page being drawn.
     *
     * THE EDITOR PREVIEWS ANY PAGE (FR-27), and the device is the only party that can resolve a
     * page's values — it holds the credentials and already fetched the documents. Resolving only
     * the drawn page meant every other page previewed as "--" until the user saved and the device
     * happened to rotate onto it, which is the reported "the values show blank til you save".
     * So the tick now resolves EVERY page, and a fetch driven by the union of their needs serves
     * all of them from one set of requests.
     *
     * PARSED ONCE, THEN DISCARDED — THE TREE MUST NOT SURVIVE THE FETCH. A cJSON tree is several
     * times the document, and holding one across the TLS handshake is the documented memory
     * hazard on this part (the handshake needs contiguous DRAM the tree would fragment). The raw
     * config string stays, and is re-parsed after the fetch to resolve each page. */
    value_needs_t needs;
    memset(&needs, 0, sizeof(needs));
    /* The HA entities the WHOLE document needs, in first-seen order — the order the template
     * request is built in and the order a widget's slot is looked up in, so they must agree. */
    char ha_ids[LAYOUT_MAX_FIELDS][48];
    int n_ha = 0;
    if (cfg_ok) {
        cJSON *root = cJSON_Parse(cfg_json);
        if (root) {
            const int np = cfg.page_count > 0 ? cfg.page_count : 1;
            layout_scan_all_pages(root, np,
                                  &needs.need_owm_current, &needs.need_owm_daily,
                                  &needs.need_owm_alert, &needs.need_ha, &needs.max_day_index,
                                  ha_ids, LAYOUT_MAX_FIELDS, &n_ha);
            cJSON_Delete(root);
        }
    }
    HEAP_DIAG("after config scan");

    fetch_creds_t creds;
    read_creds(&creds);

    /* FR-6: which product will ACTUALLY be fetched.
     *
     * Resolved ONCE, here, and used for BOTH the endpoint selection below and FR-7's alert
     * answer — so the alert bar can never describe a different product from the one the fetch
     * used, which is exactly how the bar came to announce "alerts unavailable" on a key that had
     * them.
     *
     * The probe runs only for AUTO. An explicit setting already says which product the key
     * carries, so probing would spend a call answering a question the config answered. */
    const owm_product_t product =
        (cfg.owm_product == OWM_PRODUCT_AUTO)
            ? owm_product_resolve(OWM_PRODUCT_AUTO, onecall_probe(&creds))
            : (owm_product_t)cfg.owm_product;
    const int onecall = (product == OWM_PRODUCT_ONECALL3);

    const long now_unix = (long)(esp_timer_get_time() / 1000000LL);

    /* ---- Fetch, one document per source ----
     *
     * Each fetch is independent: a forecast failure must not stop the current reading from
     * appearing, and vice versa. That is why the results are separate strings rather than one
     * blob. */
    char *forecast = NULL;
    static char ha_resp[512];
    ha_resp[0] = '\0';

    datasrc_value_t current;
    memset(&current, 0, sizeof(current));

    /* On One Call 3.0 there is NO separate current-conditions product: the one document carries
     * current, daily, and the official alerts together, so it is fetched whenever the page binds
     * any of the three. On the free tier the two 2.5 products are genuinely independent calls and
     * each is made only when the page binds something from it. */
    const int need_forecast_doc = needs.need_owm_daily || needs.need_owm_alert ||
                                  (onecall && needs.need_owm_current);
    int got_current = 0;

    /* ---- THE SPLIT INTERVAL: is OWM due, or do we reuse the last document? ----
     *
     * `owm_due` is decided ONCE for the whole OWM side (both fetches, current and forecast) so a
     * tick can never refresh one half and reuse the other — which would put a fresh temperature
     * beside a stale forecast and, worse, credit the call counter twice for one logical fetch.
     *
     * When the split is NOT active (owm_seconds == interval) this is always 1, so the code below
     * is exactly the pre-split path with one extra branch that is always taken.
     *
     * `want_owm` is whether the page needs OWM at all. When it does and OWM is due, fetch; when it
     * does and OWM is NOT due, fall through to the retained documents. */
    const int owm_due = owm_fetch_due(cfg.owm_update_seconds);
    const int want_owm = needs.need_owm_current || needs.need_owm_daily || needs.need_owm_alert;
    const int owm_fetching = want_owm && owm_due;
    const int split_active = cfg.owm_update_seconds > cfg.update_seconds;

    /* The split was turned OFF since the last tick: give the retained bytes back rather than hold
     * DRAM for a feature no longer in use. Cheap and idempotent (a NULL cache is a no-op). */
    if (!split_active && s_forecast_cache) forecast_cache_release();

    if (owm_fetching && !onecall) {
        /* The parsed current reading is used for the fetch's success and for the daily-call
         * bookkeeping (fetch_current credits the call to the response's own day); the widgets
         * then re-read the DOCUMENT rather than this one value. */
        got_current = (fetch_current(&creds, resp, sizeof(resp), &current, product) == 0);
    }

    if (owm_fetching && need_forecast_doc) {
        /* THE FINAL FORECAST DOCUMENT LIVES IN THE RETAINED BUFFER when the split is active, so a
         * later tick that skips OWM can still resolve its widgets from it. When the split is NOT
         * active there is no reason to keep it past the render, so the transient buffer is used
         * exactly as before and the memory profile is unchanged (see s_forecast_cache).
         *
         * The request is bounded to the days the page binds, so the retained size is sized to that
         * request rather than to the 40-block maximum. */
        const int days = needs.need_owm_daily ? needs.max_day_index + 1 : 0;
        const size_t need = owm_forecast_buf_bytes(days > 0 ? days * 8 : FORECAST_MAX_BLOCKS);

        if (split_active) {
            if (ensure_forecast_cache(need) == 0 && s_forecast_cache) {
                if (fetch_forecast(&creds, s_forecast_cache, s_forecast_cap, days, product) == 0) {
                    forecast = s_forecast_cache;
                    s_have_forecast_cache = 1;
                } else {
                    s_have_forecast_cache = 0;   /* keep nothing rather than a half-filled doc */
                }
            }
        } else {
            forecast = heap_caps_malloc(FORECAST_BUF_BYTES, MALLOC_CAP_8BIT);
            if (forecast) {
                if (fetch_forecast(&creds, forecast, FORECAST_BUF_BYTES, days, product) != 0) {
                    free(forecast);
                    forecast = NULL;
                }
            } else {
                /* Not fatal — the widgets show their fallback — but worth logging, because the
                 * usual reason is heap pressure and that is worth seeing. */
                ESP_LOGW(TAG, "no heap for the forecast buffer (%u bytes)",
                         (unsigned)FORECAST_BUF_BYTES);
            }
        }

        if (forecast && onecall) {
            /* The One Call document IS the current-conditions document, so the reading the rest of
             * this function treats as "did the current fetch work" comes out of it. Parsing rather
             * than assuming success: a 200 whose body did not survive the buffer is not a reading,
             * and treating it as one would cache garbage. */
            current = owm_parse_current_temp(forecast,
                                             (long)(esp_timer_get_time() / 1000000LL));
            got_current = (current.status == DATASRC_OK);
        }
    } else if (want_owm && !owm_due) {
        /* OWM IS NOT DUE: reuse the documents retained from the last fetch, so the panel keeps its
         * OWM readings while only the HA half is refreshed. If nothing has been fetched yet this
         * boot the buffers are empty and the widgets fall back to their placeholders, which is the
         * honest answer rather than a stale value. */
        if (s_have_forecast_cache && s_forecast_cache) forecast = s_forecast_cache;
        ESP_LOGI(TAG, "OWM not due (%d s); reusing the retained documents",
                 cfg.owm_update_seconds);
    }

    if (owm_fetching) s_last_owm_fetch_us = esp_timer_get_time();

    if (needs.need_ha) {
        if (fetch_ha(&creds, ha_ids, n_ha, ha_resp, sizeof(ha_resp)) != 0) {
            ha_resp[0] = '\0';
        }
    }

    /* The radio is torn down BEFORE the ADC read and before any panel work (HW-3, NFR-3) —
     * but ONLY on battery. On USB the device stays awake to serve the API (FR-31), and the
     * API is useless without a network, so the connection is kept up deliberately. */
    if (source != POWER_SOURCE_USB) {
        net_wifi_disconnect();
    }

    if (owm_fetching && !got_current) {
        /* Not fatal, and NOT a reason to skip the render: the panel still gets whatever
         * static layer is live (which is the whole point when the web app has just uploaded
         * one), with the last known reading if there is one. The error is recorded for
         * /api/status either way (FR-33).
         *
         * ONLY WHEN WE ACTUALLY TRIED. A tick that skipped OWM because the split interval had not
         * elapsed has no failure to report — recording one would fill /api/status with errors on
         * every fast HA tick, which is exactly the noise the bounded error log exists to avoid. */
        api_note_error("owm: no current reading");
        ESP_LOGW(TAG, "fetch failed; widgets fall back to their placeholders");
    } else if (got_current && !onecall) {
        /* Remember the DOCUMENT, not a formatted string: the widgets bind to different fields
         * of it (temp, humidity, wind, conditions), so caching one number would only serve
         * whichever widget happened to be first in the page.
         *
         * Only on the free tier: `resp` holds 2.5/weather there, and on One Call the current
         * conditions live in the forecast document, which is retained separately (s_forecast_cache)
         * when the split is active and must not be cached here by reference. */
        const size_t n = strlen(resp);
        if (n < sizeof(s_last_current)) {
            memcpy(s_last_current, resp, n + 1);
            s_have_last_current = 1;
        }
    }

    /* Which document the current-conditions widgets read.
     *
     * THREE SOURCES, in priority order, and the order matters:
     *   1. A document fetched THIS tick (the normal case).
     *   2. On One Call, the retained forecast document — its top-level fields ARE the current
     *      conditions, so when the split skipped the fetch it is still the right source. This is
     *      why it is checked before the 2.5/weather fallback, which is empty on One Call.
     *   3. The last good 2.5/weather document (free tier), which covers both a skipped tick and a
     *      genuinely failed fetch — an outage leaves the readings on the glass rather than
     *      replacing every one with "--". A device that has NEVER fetched has nothing here and
     *      correctly shows the placeholders. */
    const char *current_doc = NULL;
    if (got_current) {
        current_doc = onecall ? forecast : resp;
    } else if (onecall && s_have_forecast_cache && s_forecast_cache) {
        current_doc = s_forecast_cache;
    } else if (s_have_last_current) {
        current_doc = s_last_current;
        ESP_LOGI(TAG, "using the last good reading document (%u bytes)",
                 (unsigned)strlen(s_last_current));
    }

    /* Build the field/value arrays from the page's widgets. A NULL document makes the widgets
     * that needed it resolve to their own fallback rather than to a wrong number. */
    const value_sources_t src = {
        .owm_current = current_doc,
        .owm_daily   = forecast,
        .ha_line     = (needs.need_ha && ha_resp[0]) ? ha_resp : NULL,
        /* FR-7, from the RESOLVED product — the same value the fetches above used, so the bar
         * cannot describe a different product from the one on the glass. */
        .owm_alerts_supported = needs.need_owm_alert ? owm_product_has_alerts(product) : 0,
    };

    /* ---- Resolve EVERY page for GET /api/values (FR-27) ----
     *
     * This is what makes the editor's preview show real values for the page it is editing, even
     * while the glass is on another page (see the scan above). Each page is resolved into the
     * SAME tick-local buffer in turn, so the ~9 KB page_render_t is not duplicated per page;
     * only the drawn page's result is left in `page` at the end, which is what the render reads.
     *
     * Recorded even for a failed fetch: the widget then resolved to its fallback, and "the panel
     * will show --" IS the honest answer rather than a stale value from a previous refresh.
     *
     * ONE PARSE FOR EVERY PAGE. The tree is several times the document on this part, so parsing it
     * once per page would be the dominant cost of the pass — and the tree is safe to hold HERE
     * because the fetch and the TLS handshake are already behind us (the hazard is holding it
     * ACROSS the handshake, which the scan above avoids by freeing its tree before the fetch).
     *
     * The drawn page is resolved LAST so its built fields/values are the ones the push below
     * stamps. Reading it through the same path means the preview and the glass cannot disagree —
     * a preview produced by different code is exactly the "preview is a confident lie" failure
     * FR-27 and NFR-4 exist to prevent. */
    const int page_total = cfg_ok && cfg.page_count > 0 ? cfg.page_count : 1;

    /* Size the per-page value store BEFORE anything records into it, and allocate it HERE rather
     * than in .bss — a fixed LAYOUT_MAX_PAGES x 24 array is ~13 KB of DRAM the heap never gets,
     * which measured before as enough to drop the largest free block below what the static layer
     * needs. See api_values_reserve. This is still before the render window takes the layer, so it
     * does not compete for the contiguous block the layer needs. */
    api_values_reserve(page_total);

    if (cfg_ok) {
        cJSON *root = cJSON_Parse(cfg_json);
        if (root) {
            /* Every page EXCEPT the drawn one is recorded first; the drawn page is resolved last so
             * its fields/values are what `page` holds for the push below. Resolving it in the same
             * loop would let a later page overwrite it, and the panel would then stamp another
             * page's readings into this page's boxes. */
            for (int p = 0; p < page_total; p++) {
                if (p == page_index) continue;
                memset(&page, 0, sizeof(page));
                page.n = layout_widgets_from_root(root, p, page.widgets, LAYOUT_MAX_FIELDS);
                if (page.n < 0) page.n = 0;
                build_fields(&page, &src, ha_ids, n_ha, now_unix);
                api_record_values(page.ids, page.values, page.has_value,
                                  page.rendered_number, page.readings,
                                  page.n_fields, p, page_total);
            }

            memset(&page, 0, sizeof(page));
            page.n = layout_widgets_from_root(root, page_index, page.widgets, LAYOUT_MAX_FIELDS);
            if (page.n < 0) page.n = 0;
            build_fields(&page, &src, ha_ids, n_ha, now_unix);
            api_record_values(page.ids, page.values, page.has_value,
                              page.rendered_number, page.readings,
                              page.n_fields, page_index, page_total);
            cJSON_Delete(root);
        }
    } else {
        /* No config: still stamp the fallbacks, so a page with no document resolves rather than
         * keeping whatever a previous refresh left in `page`. */
        memset(&page, 0, sizeof(page));
        build_fields(&page, &src, ha_ids, n_ha, now_unix);
    }

    /* The config string has served every reader above; give it back now so the render window opens
     * against the same heap it would have without the per-page pass. */
    free(cfg_json);
    cfg_json = NULL;

    /* The forecast buffer has served its purpose; releasing it here gives the render window the
     * ~16.5 KB back, which matters on USB where the second framebuffer is already tight.
     *
     * THE RETAINED CACHE IS NOT FREED. When the split is active, `forecast` points at
     * s_forecast_cache and freeing it here would both lose the document the next skipped tick must
     * reuse AND leave s_forecast_cache a dangling pointer. Only the transient (non-split) buffer is
     * released, which is the pre-split behaviour exactly. */
    if (forecast && forecast != s_forecast_cache) {
        free(forecast);
    }
    forecast = NULL;
    HEAP_DIAG("after forecast free");

    /* The TLS worker's stack headroom, in the trace build only. net_http_stack_hwm() has existed
     * since the TLS work but nothing ever READ it, so NET_TLS_TASK_STACK's former 16 KB was never
     * justified by the measurement its own comment demands — and that 16 KB was a contiguous DRAM
     * allocation competing with the 78,200-byte framebuffer in this very window. Printing it here
     * is what makes shrinking the stack an evidence-based change rather than a gamble. */
#if HEAP_TRACE
    ESP_LOGI("heaptrace", "%-28s %u bytes of stack never touched",
             "tls stack headroom", net_http_stack_hwm());
#endif

    /* Decide full vs partial through the TESTED policy, never an inline comparison.
     *
     * The limit comes from the config THIS TICK ALREADY PARSED, not from api_partial_limit().
     * That function re-reads the stored document through cfg_store_get(), which mallocs the full
     * 16,384-byte CFG_JSON_MAX_LEN block — and this line is INSIDE the render window, in the gap
     * between releasing the static layer and re-acquiring it. A transient 16 KB block landing in
     * the freshly-freed 78 KB hole is precisely the fragmentation that makes the re-acquire fail,
     * which is silent on the glass. Measured with HEAP_TRACE: the window opens with one clean
     * 110,592-byte block, and that is the whole margin the layer needs.
     *
     * `cfg` is already parsed above and layout_config_parse() seeds the same default (5) and the
     * same clamp, so this is the identical number with no allocation. */
    const int limit = cfg.partial_refresh_limit;
    /* A caller-supplied `force_full` is for the case where the caller KNOWS the frame on the
     * glass is no longer a valid diff base (a layout/bitmap change). The pending request flag
     * is read here as before, so the periodic mains refresh — which passes 0 — still gets the
     * ordinary partial/full decision instead of flickering a full refresh every interval. */
    const int forced_full = force_full || api_take_full_refresh();
    /* "Nothing on the glass" is tracked separately from the partial counter: the counter is
     * reset to 0 BY a full refresh, so treating 0 as "nothing drawn" would make every
     * refresh a full one and kill the partial path entirely.
     *
     * IT IS ITS OWN FLAG, NOT A TEST ON THE SLOT'S SIGN. The artwork identity is a NEGATIVE
     * sentinel (negative for every real uploaded layout), so `s_shown_slot < 0` was true for every device with an uploaded
     * layout — every tick read "nothing on the glass" and forced a full refresh, which is why
     * /api/status reported partials_since_full: 0 regardless of the partial budget. The two
     * questions ("is there anything to diff against" and "is it the same picture") are separate
     * and are now answered separately. */
    const int nothing_on_glass = !s_glass_present;
    /* The datasheet's 24 h rule, from real elapsed time — see hours_since_full(). Passing a
     * constant 0 here would silently disable it, which is the one policy that protects the
     * panel from permanent ghosting. */
    refresh_kind_t kind = refresh_decide(nothing_on_glass, api_partials_since_full(),
                                         limit, hours_since_full());
    if (forced_full) kind = REFRESH_FULL;

    /* ---- The render window: re-acquire the static layer ----
     *
     * The layer is taken HERE, after the fetch and after net_wifi_disconnect(), because that is
     * when the region it needs is most likely to be free — see the release note at the top of this
     * function. It is REQUIRED rather than a preference: without it nothing can be composed, so a
     * failure fails the tick and leaves the last good image on the glass (FR-29).
     *
     * This is the ONE whole-panel buffer the push needs. The previous and next frames are composed
     * a band at a time out of it (see push_banded), which is what makes FR-11's partial path
     * reachable on this part at all — the old design asked for a SECOND 78,200-byte framebuffer
     * here, which never fitted, so every refresh fell back to a full flash and the partial path
     * was dead code that reported success.
     *
     * The wait inside ensure_static() is what makes this reliable on USB — see its comment for why
     * the region is briefly unusable and how long it takes to clear. The slot identity is NOT
     * cleared, so a partial whose picture is still on the glass remains available. */
    HEAP_DIAG("before static layer acquire");
    if (ensure_static() != 0) {
        /* Flag it so the serve loop retries shortly instead of holding the stale image for a
         * full interval; the flag is the only signal, since the image on the glass is
         * deliberately untouched.
         *
         * The BOTH-numbers profile is carried in the message because /api/status is the field
         * diagnostic (FR-33) and there is no console in the field: `largest_free_block` is the
         * number that predicts whether the next acquire can succeed, and pairing it with the
         * total tells "fragmented" (total high, largest low) from "genuinely out of memory"
         * (both low) without a re-flash. ensure_static() has already waited FB_ACQUIRE_WAIT_MS
         * for a transient fragmenter to clear before this point is reached. */
        s_fb_lost = 1;
        char _m[80];
        snprintf(_m, sizeof(_m), "render: no static layer (free %u, largest %u)",
                 (unsigned)esp_get_free_heap_size(),
                 (unsigned)heap_caps_get_largest_free_block(MALLOC_CAP_8BIT));
        api_note_error(_m);
        return;
    }
    s_fb_lost = 0;
    HEAP_DIAG("after static layer acquire");

    /* Pull the static layer into the resident SEGMENTED buffer. This is the ONLY whole-panel buffer
     * held: the previous and the next FRAME are each produced a band at a time from it by
     * push_banded(), which is what makes a partial possible on this part (see the block comment on
     * the layer). */
    int slot = SLOT_NONE;
    if (load_static_layer_seg(&s_layer, page_index, &slot) != 0) {
        ESP_LOGE(TAG, "no static layer for page %d", page_index);
        return;
    }
    /* The strip decoder has done its job — give the ~11 KB back before the band buffers are taken,
     * so the push has the room. ensure_static() re-reserves it on the next tick. */
    artwork_inflate_release(s_inflate);
    s_inflate = NULL;
    /* The panel may be in deep sleep (the boot path sleeps it after showing the last good
     * image, and the USB serve loop then keeps running). Drawing to a sleeping controller
     * does not fail cleanly — it times out on BUSY, which is indistinguishable from a loose
     * FPC. Waking is a no-op when it is already awake.
     *
     * EVERY EXIT BELOW THE WAKE MUST PUT THE PANEL BACK TO SLEEP, because FR-12 requires the
     * controller not be left powered between updates. A bare `return` leaves it powered until the
     * next tick — and when the reason for returning is a thermal block, the next tick blocks on the
     * same condition, so the panel would sit powered indefinitely. The image is bistable and
     * survives the sleep, so sleeping costs nothing visible. */
    if (epd_wake() != ESP_OK) {
        ESP_LOGE(TAG, "panel did not wake");
        api_note_error("render: panel did not wake");
        /* DELIBERATELY NOT followed by epd_sleep(), unlike the exits below. A failed wake means the
         * panel is not answering, and epd_sleep()'s own BUSY wait is bounded at 20 s — stacking a
         * second 20-second block on an unresponsive panel would stall the serve loop for 40 s per
         * tick while making the panel no safer to leave alone. Nothing was drawn, so the next tick
         * re-inits from scratch regardless. */
        return;
    }

    /* HW-1: do not draw outside the panel's 0..50 C operating range. Checked HERE, after
     * epd_wake() and before the push, because the guard's read of the controller's temperature is
     * an SPI command that only answers on an awake panel — reading it earlier would make the
     * guard always come back UNKNOWN. Nothing is drawn to a panel outside its range: that is
     * exactly the "garbage on the glass" HW-1 forbids.
     *
     * This logs, and records THROUGH api_note_error, which is /api/status's evidence that a
     * refresh was suppressed and why (FR-33). */
    if (thermal_blocks_render()) {
        epd_sleep();
        return;
    }

    /* A partial is only valid when the frame on the glass came from the SAME static layer and
     * the SAME values we still hold: the controller derives each pixel's transition from the
     * previous/next pair, so diffing against a frame this firmware cannot reproduce would leave
     * ghosted fragments of an unrelated picture. `s_shown_slot` is the picture's identity (see
     * load_static_layer_seg) and `s_have_prev_values` says the previous values were recorded.
     *
     * `actual_partial` is recorded rather than re-derived at the log below. An earlier version
     * recomputed "partial" from `kind` alone, which is the DECISION and not the ACTION: when the
     * previous frame could not be reproduced the decision was still PARTIAL while a full refresh
     * ran, so the log said "partial refresh done" and every FR-11 check read that as a partial. */
    int actual_partial = (kind == REFRESH_PARTIAL && s_shown_slot == slot &&
                          s_have_prev_values);

    /* THE PANEL'S WAVEFORM IS THE DRIVER'S BUSINESS, and it enforces it inside every writer
     * (epd_ensure_waveform): a partial is drawn with the PARTIAL OTP waveform and a full with the
     * temperature-compensated LUT ladder, and the two are NOT interchangeable. Driving the
     * controller in one mode while sending the other mode's stream is silent on the wire — the
     * bytes are accepted and the panel shows something, just wrong (grey, half-transitioned pixels
     * where a value changed) — so the check belongs where the register state is known, not at this
     * call site. There were two reasons FR-11's partial path had never run at all: the second
     * framebuffer never allocated (now replaced by band composition), and epd_init_partial() was
     * never called. The driver now does both correctly on its own.
     *
     * A waveform failure therefore surfaces here as a failed push, which is handled below: the image
     * stays as it was and the error is recorded for /api/status (FR-33). */
    const frame_spec_t next = {
        .fields = page.fields, .values = page.value_ptrs, .n_fields = page.n_fields,
    };
    const frame_spec_t prev = {
        .fields = s_prev_values.fields, .values = s_prev_values.value_ptrs,
        .n_fields = s_prev_values.n_fields,
    };

    e = push_banded(&next, &prev, actual_partial);
    if (e != ESP_OK) {
        ESP_LOGE(TAG, "panel update failed: %s", esp_err_to_name(e));
        api_note_error("render: panel update failed");
        /* A NO-MEM failure here is a heap problem, not a panel problem, and it is transient in the
         * same way a failed layer acquire is: the region is fragmented by small network allocations
         * that free on their own. Measured on USB before the adaptive band size existed, the band
         * buffer missed by 792 bytes on EVERY tick for several minutes — the panel kept a stale
         * reading the whole time, with nothing retrying it until the next 15-minute interval. Flag
         * it so the serve loop comes back in seconds. */
        if (e == ESP_ERR_NO_MEM) s_fb_lost = 1;
        epd_sleep();        /* FR-12: never leave the controller powered (see the note above) */
        return;
    }

    /* The values just drawn are the ones a LATER partial must reproduce for its "previous" frame,
     * so they are recorded only after the push succeeded. `slot` too: it identifies the picture,
     * and a slot recorded against a frame that never made it to the glass would authorise a
     * partial against the wrong base.
     *
     * THE STRINGS ARE COPIED INTO THE SNAPSHOT'S OWN STORAGE AND THE POINTERS REBASED, which is not
     * incidental. `page.value_ptrs[i]` points into `page.values[i]` — the TICK-LOCAL page, which the
     * next tick overwrites. Copying the pointers would leave the snapshot pointing at the NEW
     * values, so the "previous" frame would be composed with the very values it is meant to differ
     * from, the two frames would be identical, and the partial would write nothing to the glass
     * while reporting success. Rebasing onto the snapshot's own storage is what makes it a
     * snapshot. */
    s_prev_values.n_fields = page.n_fields;
    for (int i = 0; i < page.n_fields; i++) {
        s_prev_values.fields[i] = page.fields[i];
        memcpy(s_prev_values.values[i], page.values[i], sizeof(s_prev_values.values[i]));
        s_prev_values.value_ptrs[i] = s_prev_values.values[i];
    }
    s_shown_slot = slot;
    s_glass_present = 1;
    s_have_prev_values = 1;

    if (actual_partial) {
        api_record_refresh(0);
    } else {
        api_record_refresh(1);
        /* Only a full refresh restarts the 24 h clock: a partial does not clear ghosting, so it
         * cannot postpone the need for one. */
        s_last_full_us = esp_timer_get_time();
    }
    api_record_page(page_index);
    /* The frame is on the glass, so a page override that produced THIS frame has been honoured and
     * can be cleared. It is deliberately cleared here and not when it was read, so a tick that
     * failed to draw (and returned early above) leaves the request pending for the retry. The
     * honoured page is passed so a request that arrived mid-render survives. */
    if (page_forced) api_clear_page(page_index);
    ESP_LOGI(TAG, "%s refresh done: page %d, %d fields",
             actual_partial ? "partial" : "full",
             page_index, page.n_fields);

    /* Back to deep sleep (FR-12). The image is bistable and survives it, and leaving the
     * controller powered costs current for no benefit. On battery the device deep-sleeps
     * immediately after this anyway, so this only matters for the USB serve loop. */
    epd_sleep();
}

void app_refresh_tick(power_source_t source, int force_full)
{
    /* THE WHOLE TICK HOLDS THE LAYER LOCK. That is what makes app_fetch_pause() (used by the
     * OTA path) correct: a pause waits for a tick in flight to finish, and no tick can start
     * while the layer is paused. Without it the OTA fetch would free memory this task is
     * mid-way through reading, and the render would compose from freed segments. */
    layer_lock();
    refresh_tick_locked(source, force_full);
    layer_unlock();
}
